mcihangir/camtracker/04_Hardware/PCBs/CamTracker/KiCad_Libs/Components/EMPA/empa_.png

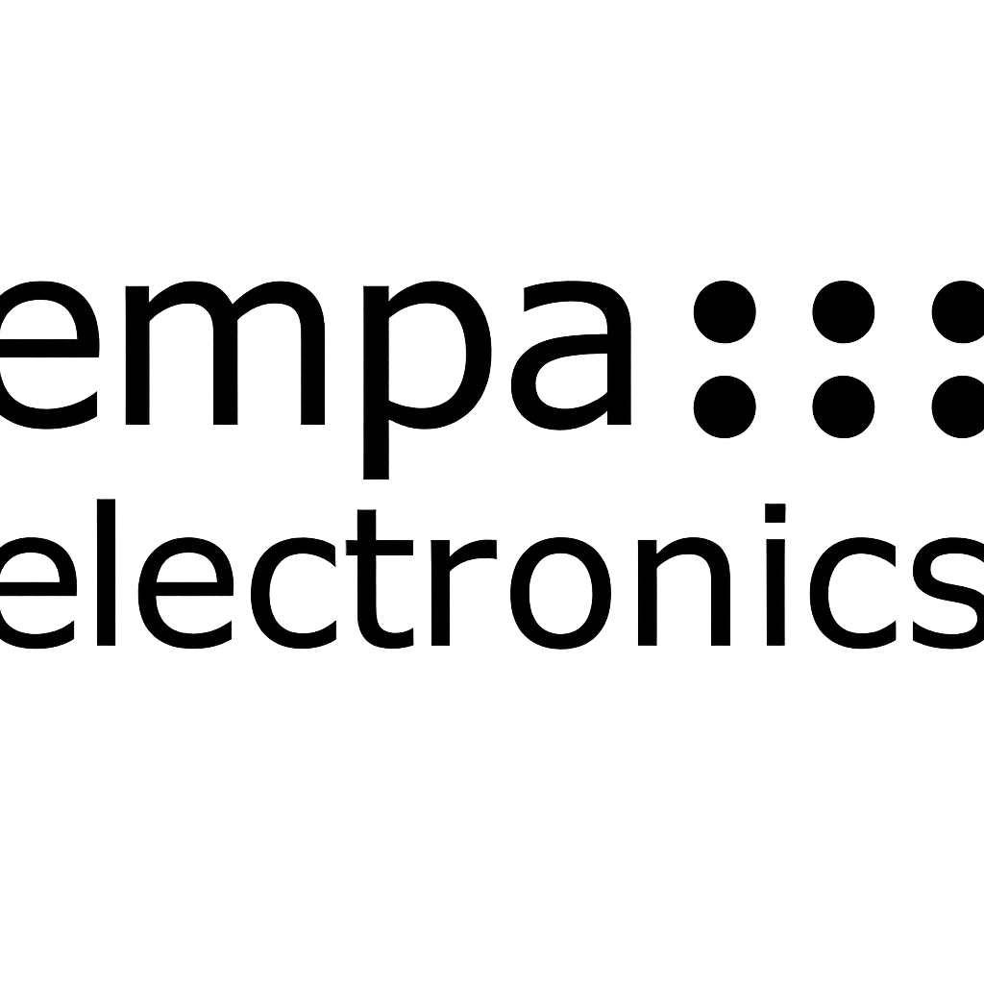
04_Hardware/PCBs/CamTracker/KiCad_Libs/Components/EMPA/empa_.png
