mcihangir/camtracker/04_Hardware/PCBs/CamTracker/KiCad_Libs/Components/C0603C751F5GACTU/3D/C0603C751F5GACTU.stp

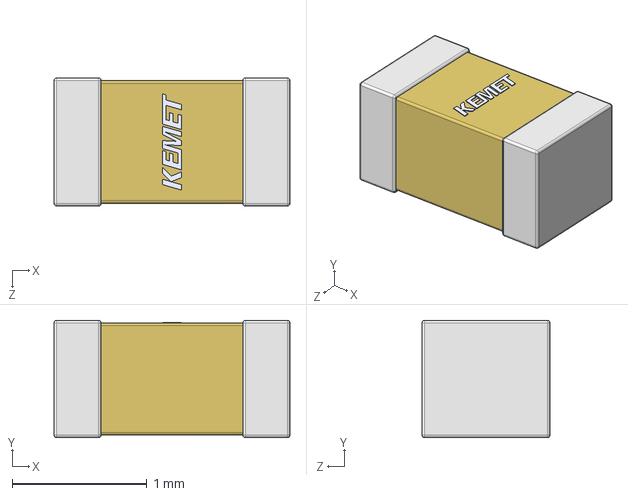
[picture p26: CAD file, 2025-10-18]
04_Hardware/PCBs/CamTracker/KiCad_Libs/Components/C0603C751F5GACTU/3D/C0603C751F5GACTU.stp
1.75 x 0.87 x 0.95 mm
