mcihangir/camtracker/04_Hardware/PCBs/CamTracker/KiCad_Libs/Components/C1608C0G1H102F080AA/3D/C1608C0G1H102F080AA.stp

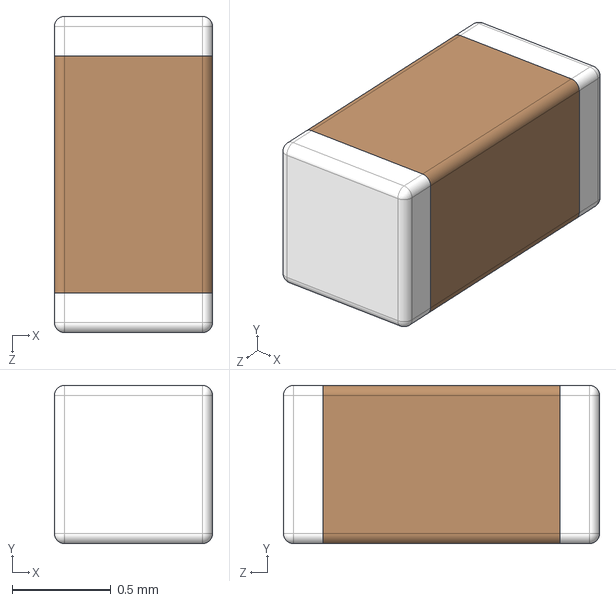
[picture p27: CAD file, 2025-10-18]
04_Hardware/PCBs/CamTracker/KiCad_Libs/Components/C1608C0G1H102F080AA/3D/C1608C0G1H102F080AA.stp
0.8 x 0.8 x 1.60 mm
