mcihangir/camtracker/04_Hardware/PCBs/CamTracker/KiCad_Libs/Components/CRCW08050000Z0EA/3D/CRCW08050000Z0EA.stp

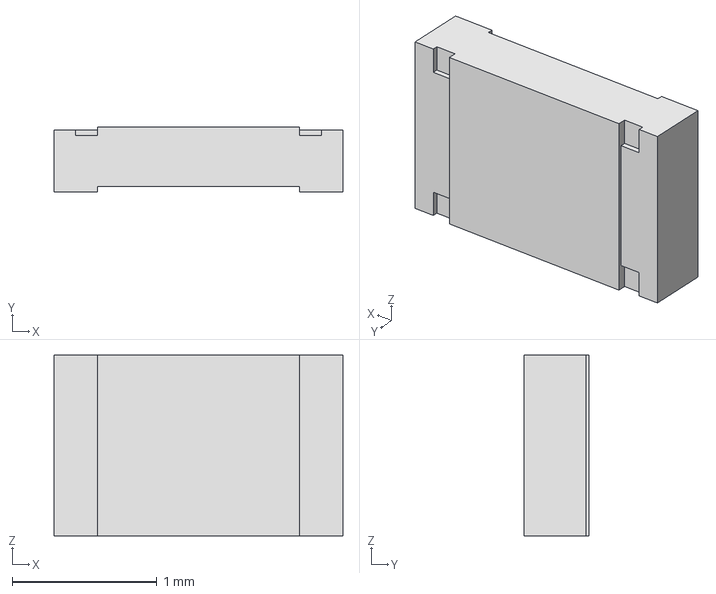
[picture p28: CAD file, 2025-10-18]
04_Hardware/PCBs/CamTracker/KiCad_Libs/Components/CRCW08050000Z0EA/3D/CRCW08050000Z0EA.stp
2.00 x 0.45 x 1.25 mm
