mcihangir/camtracker/04_Hardware/PCBs/CamTracker/KiCad_Libs/Components/CS12ANW03/CS12ANW03/3D/CS12ANW03.stp

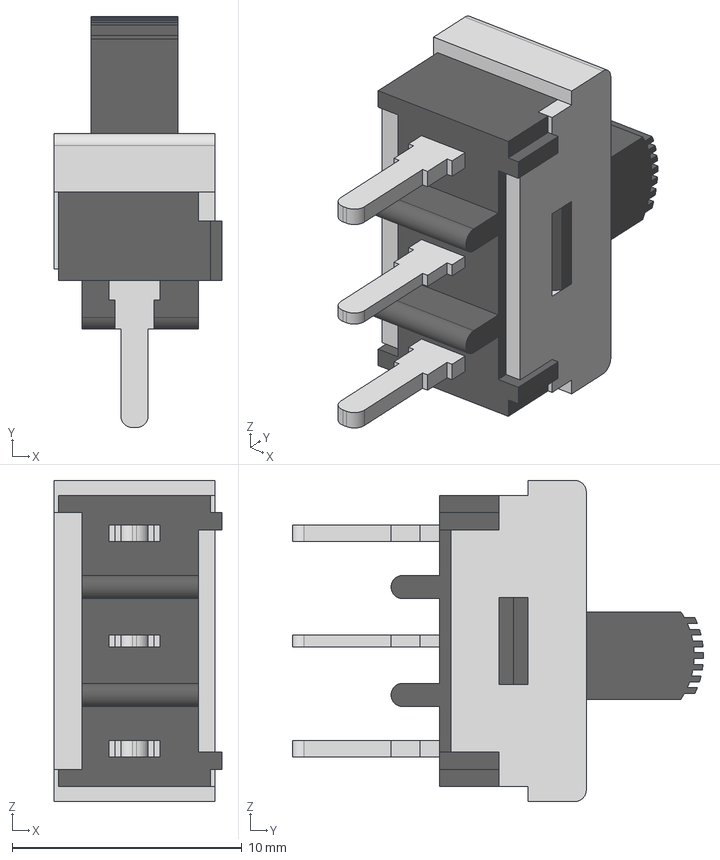
[picture p29: CAD file, 2025-10-18]
04_Hardware/PCBs/CamTracker/KiCad_Libs/Components/CS12ANW03/CS12ANW03/3D/CS12ANW03.stp
7.32 x 17.9 x 14.0 mm
CS12ANW03-body
CS12ANW03-top
CS12ANW03-term
CS12ANW03-slide
