mcihangir/camtracker/04_Hardware/PCBs/CamTracker/KiCad_Libs/Components/ERJ-3GEYJ222V/3D/ERJ-3GEYJ222V.stp

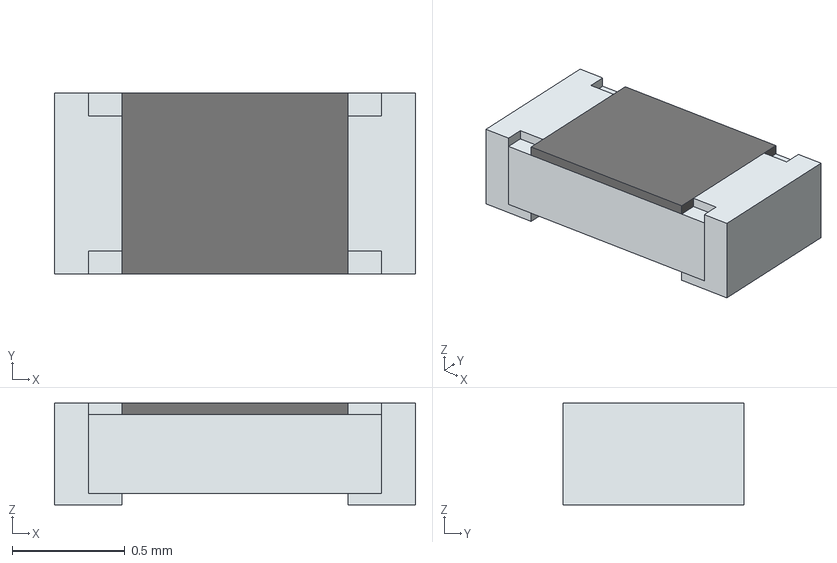
[picture p30: CAD file, 2025-10-18]
04_Hardware/PCBs/CamTracker/KiCad_Libs/Components/ERJ-3GEYJ222V/3D/ERJ-3GEYJ222V.stp
1.60 x 0.8 x 0.45 mm
solidBody
Terminal
solidTop
