mcihangir/camtracker/04_Hardware/PCBs/CamTracker/KiCad_Libs/Components/ESD9B5.0ST5G/ESD9B5.0ST5G.step

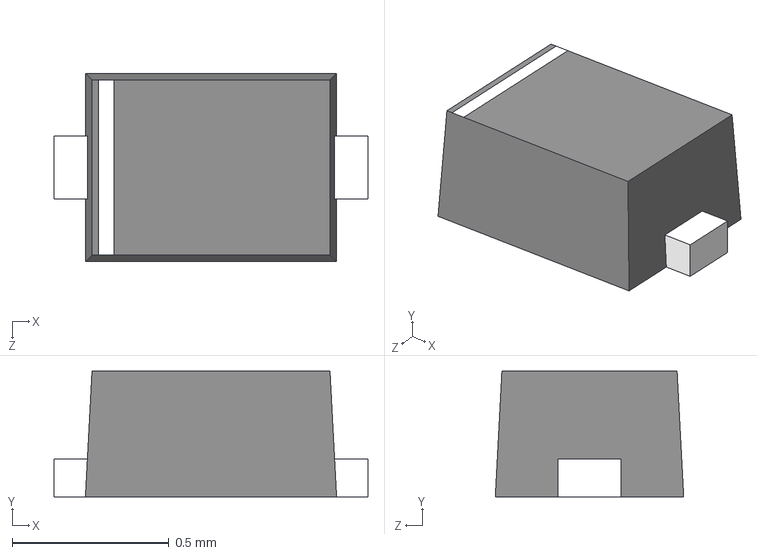
[picture p31: CAD file, 2025-10-18]
04_Hardware/PCBs/CamTracker/KiCad_Libs/Components/ESD9B5.0ST5G/ESD9B5.0ST5G.step
1 x 0.4 x 0.6 mm
