mcihangir/camtracker/04_Hardware/PCBs/CamTracker/KiCad_Libs/Components/FH12-8S-0.5SH_55_/3D/FH12-8S-0.5SH.stp

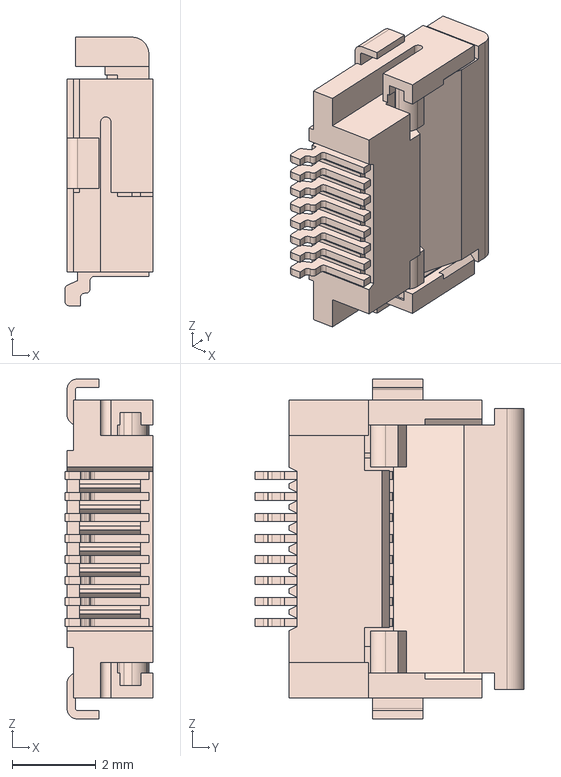
[picture p33: CAD file, 2025-10-18]
04_Hardware/PCBs/CamTracker/KiCad_Libs/Components/FH12-8S-0.5SH_55_/3D/FH12-8S-0.5SH.stp
2.10 x 6.40 x 8.10 mm
