mcihangir/camtracker/04_Hardware/PCBs/CamTracker/KiCad_Libs/Components/FH12S-30S-0.5SH_55_/3D/FH12S-30S-0.5SH_55_.stp

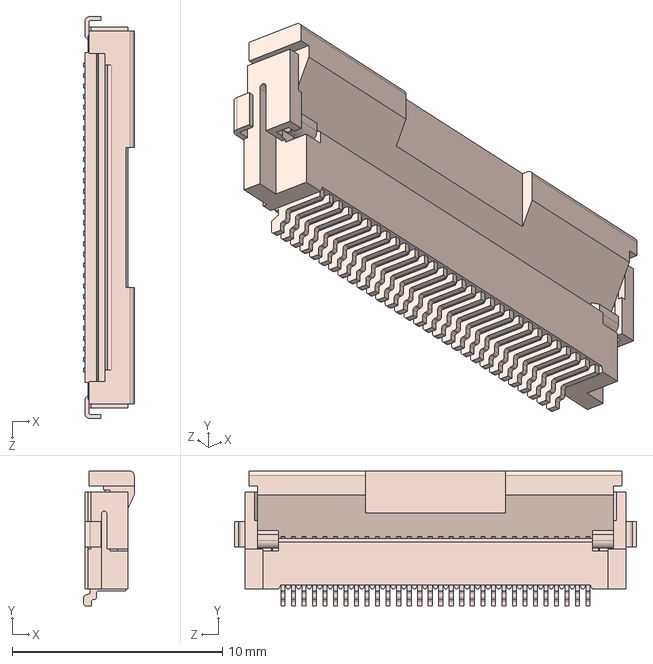
[picture p34: CAD file, 2025-10-18]
04_Hardware/PCBs/CamTracker/KiCad_Libs/Components/FH12S-30S-0.5SH_55_/3D/FH12S-30S-0.5SH_55_.stp
2.40 x 6.40 x 19.1 mm
