mcihangir/camtracker/04_Hardware/PCBs/CamTracker/KiCad_Libs/Components/FH19C-20S-0.5SH_10_/3D/FH19C-20S-0.5SH_10_.stp

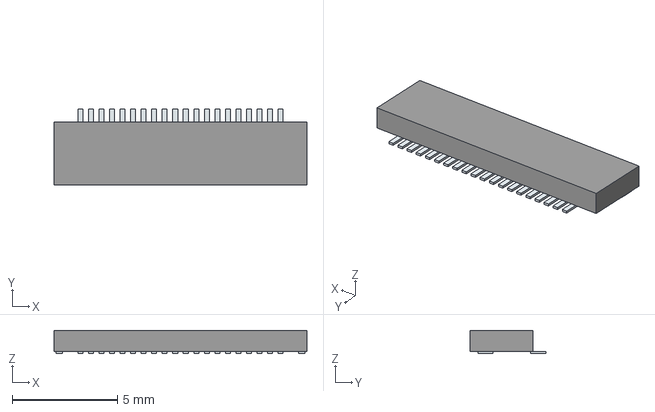
[picture p35: CAD file, 2025-10-18]
04_Hardware/PCBs/CamTracker/KiCad_Libs/Components/FH19C-20S-0.5SH_10_/3D/FH19C-20S-0.5SH_10_.stp
12.0 x 3.62 x 1.10 mm
Pins
