mcihangir/camtracker/04_Hardware/PCBs/CamTracker/KiCad_Libs/Components/FH19SC-30S-0.5SH_09_/3D/FH19C-30S-0.5SH_10_.stp

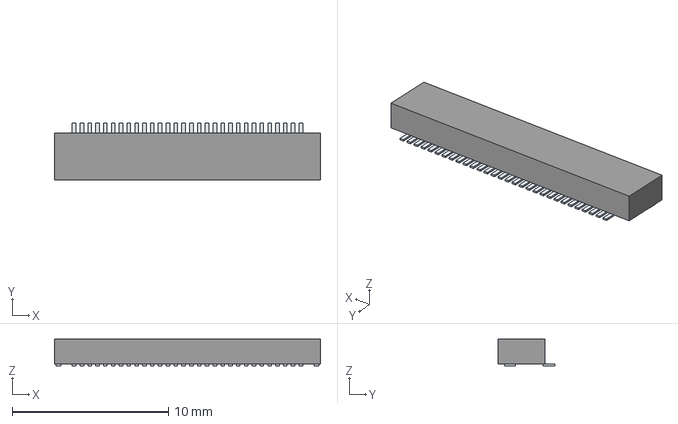
[picture p37: CAD file, 2025-10-18]
04_Hardware/PCBs/CamTracker/KiCad_Libs/Components/FH19SC-30S-0.5SH_09_/3D/FH19C-30S-0.5SH_10_.stp
17.0 x 3.62 x 1.70 mm
Pins
