mcihangir/camtracker/04_Hardware/PCBs/CamTracker/KiCad_Libs/Components/FH35C-27S-0.3SHW_50_/3D/FH35C-27S-0.3SHW-50---3DModel-STEP-1.STEP

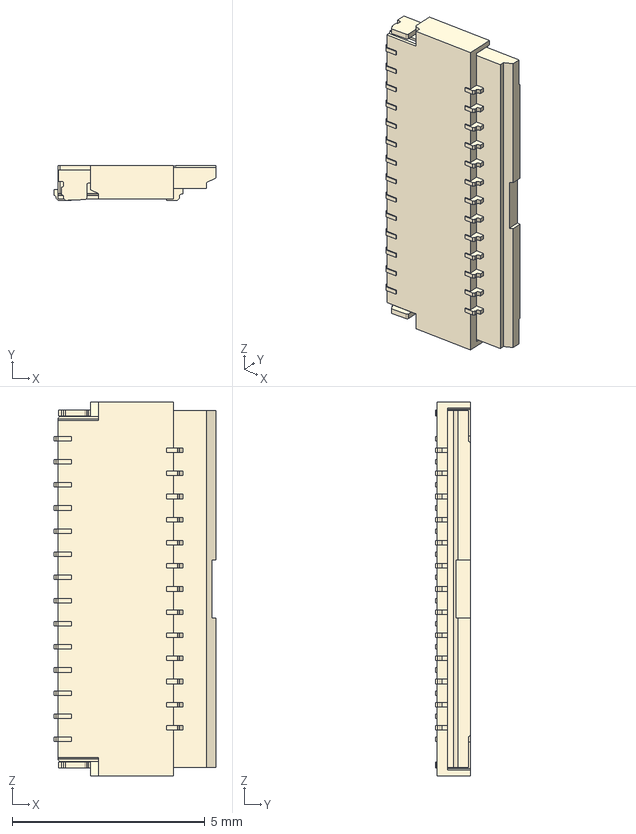
[picture p38: CAD file, 2025-10-18]
04_Hardware/PCBs/CamTracker/KiCad_Libs/Components/FH35C-27S-0.3SHW_50_/3D/FH35C-27S-0.3SHW-50---3DModel-STEP-1.STEP
4.20 x 0.9 x 9.70 mm
