mcihangir/camtracker/04_Hardware/PCBs/CamTracker/KiCad_Libs/Components/GRM1555C1H100JA01D/3D/GRM1555C1H100JA01D.stp

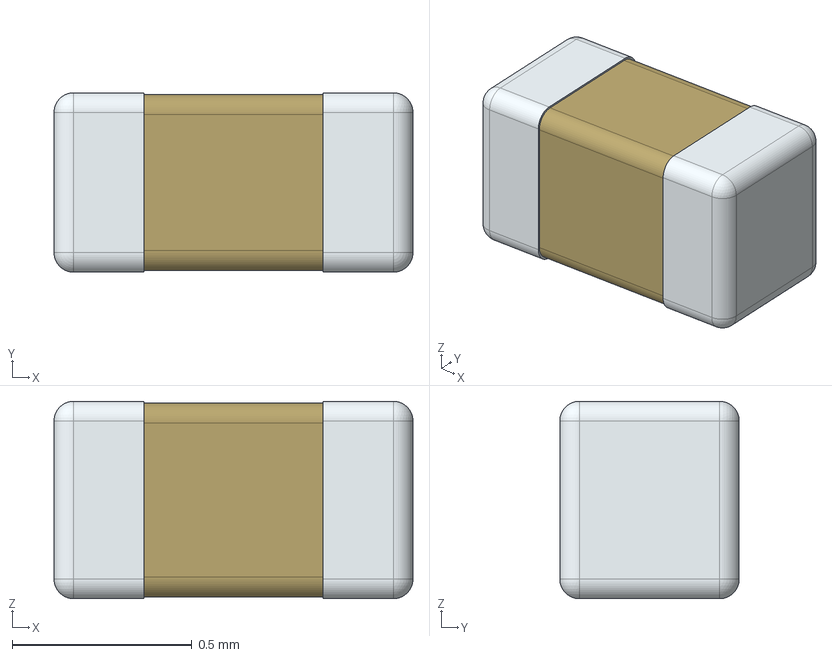
[picture p39: CAD file, 2025-10-18]
04_Hardware/PCBs/CamTracker/KiCad_Libs/Components/GRM1555C1H100JA01D/3D/GRM1555C1H100JA01D.stp
1.00 x 0.5 x 0.55 mm
