mcihangir/camtracker/04_Hardware/PCBs/CamTracker/KiCad_Libs/Components/GRM155R60J475ME47D/3D/GRM155R60J475ME47D.stp

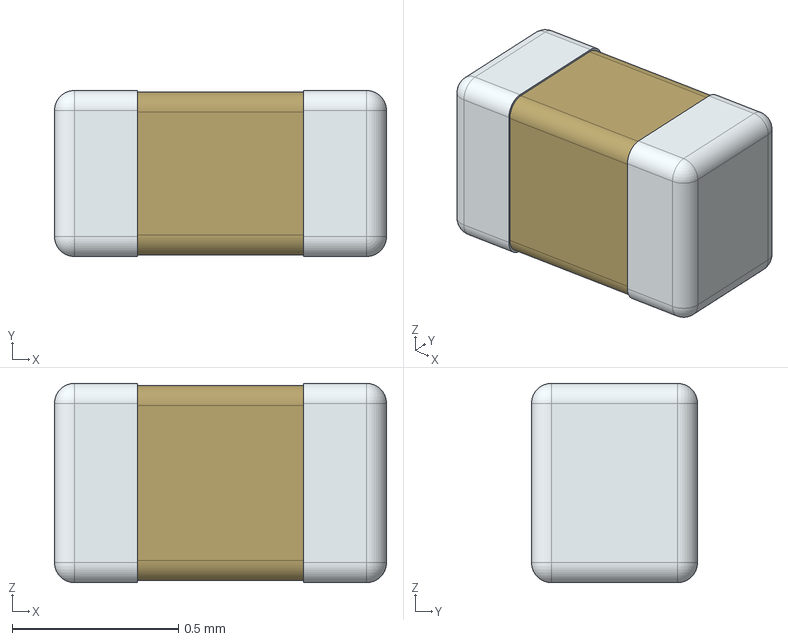
[picture p40: CAD file, 2025-10-18]
04_Hardware/PCBs/CamTracker/KiCad_Libs/Components/GRM155R60J475ME47D/3D/GRM155R60J475ME47D.stp
1.00 x 0.5 x 0.6 mm
