mcihangir/camtracker/04_Hardware/PCBs/CamTracker/KiCad_Libs/Components/GRM155R61H105KE05D/3D/GRM155R61H105KE05D.stp

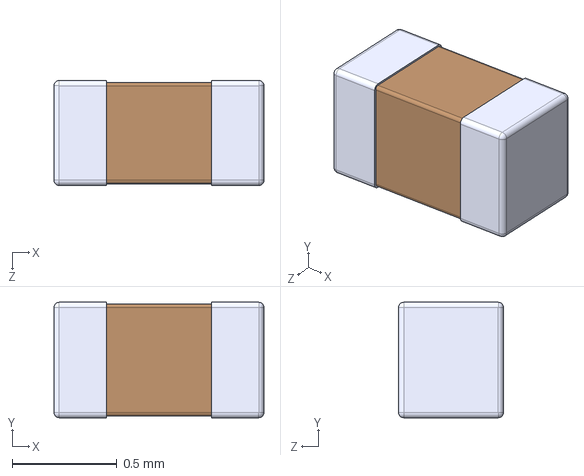
[picture p41: CAD file, 2025-10-18]
04_Hardware/PCBs/CamTracker/KiCad_Libs/Components/GRM155R61H105KE05D/3D/GRM155R61H105KE05D.stp
1.00 x 0.55 x 0.5 mm
