mcihangir/camtracker/04_Hardware/PCBs/CamTracker/KiCad_Libs/Components/GRM21BR61E226ME44L/3D/GRM21BR61E226ME44L.stp

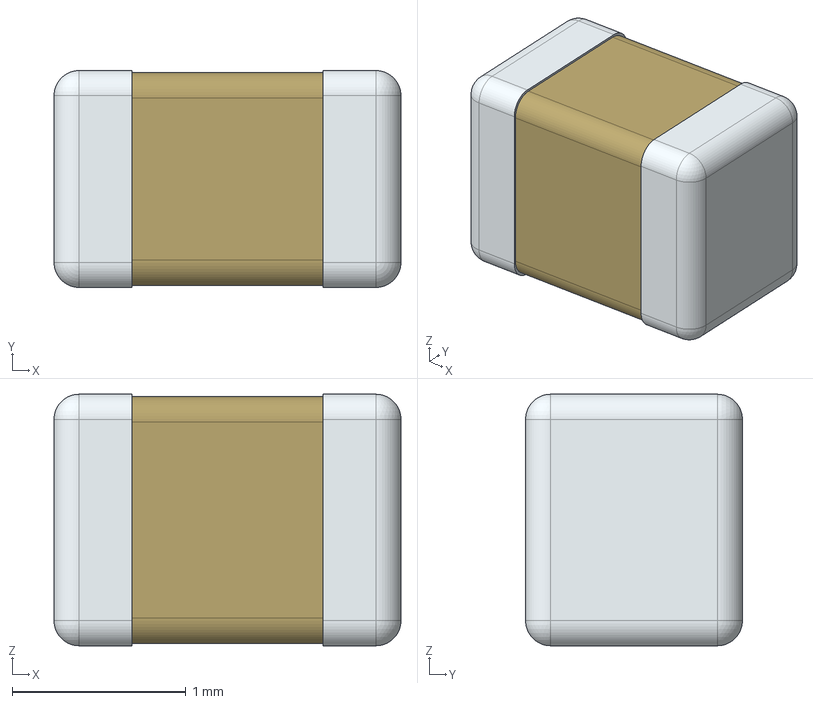
[picture p42: CAD file, 2025-10-18]
04_Hardware/PCBs/CamTracker/KiCad_Libs/Components/GRM21BR61E226ME44L/3D/GRM21BR61E226ME44L.stp
2.00 x 1.25 x 1.45 mm
