mcihangir/camtracker/04_Hardware/PCBs/CamTracker/KiCad_Libs/Components/GRM31CR60J476ME19L/3D/GRM31CR60J476ME19L.stp

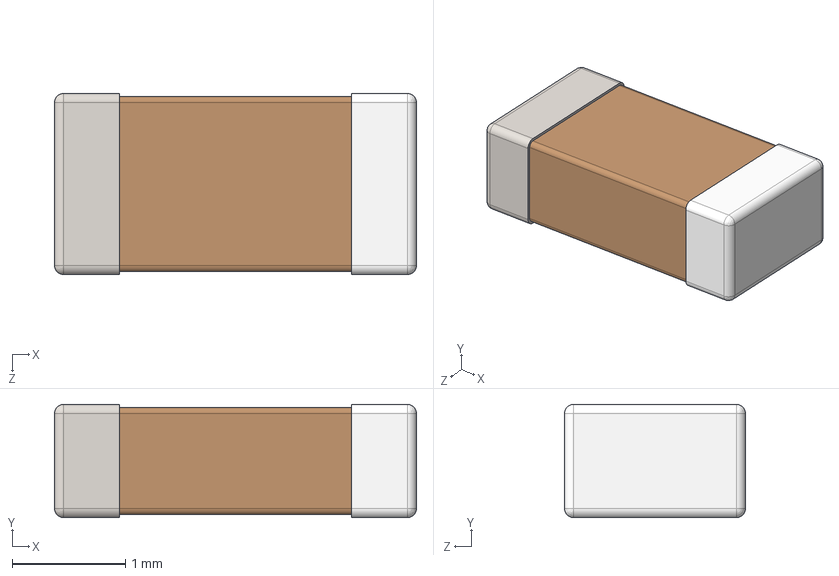
[picture p43: CAD file, 2025-10-18]
04_Hardware/PCBs/CamTracker/KiCad_Libs/Components/GRM31CR60J476ME19L/3D/GRM31CR60J476ME19L.stp
3.20 x 1 x 1.60 mm
GCM31A5C2J820JX01J_3
GCM31A5C2J820JX01J_2
GCM31A5C2J820JX01J
