mcihangir/camtracker/04_Hardware/PCBs/CamTracker/KiCad_Libs/Components/HD-EMB1104-SM-2/HD-EMB1104-SM-2.step

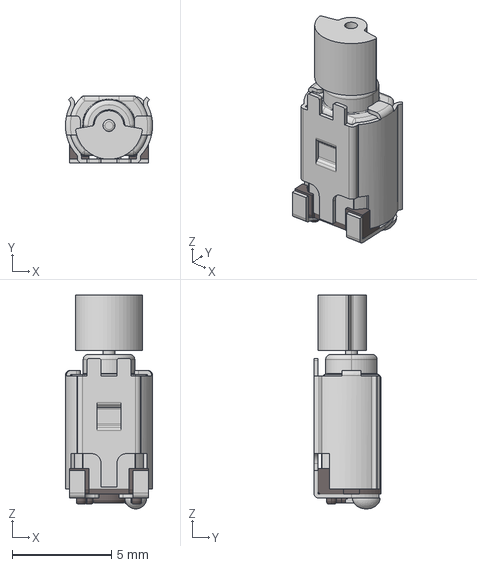
[picture p44: CAD file, 2025-10-18]
04_Hardware/PCBs/CamTracker/KiCad_Libs/Components/HD-EMB1104-SM-2/HD-EMB1104-SM-2.step
4.40 x 3.40 x 10.8 mm
