mcihangir/camtracker/04_Hardware/PCBs/CamTracker/KiCad_Libs/Components/HX JN1.27-2x10 TP H4.9/User Library-KLS1-202C-20-T-B.STEP

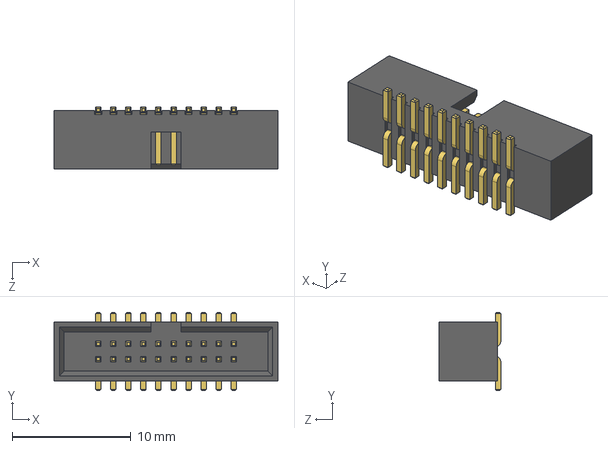
[picture p45: CAD file, 2025-12-15]
04_Hardware/PCBs/CamTracker/KiCad_Libs/Components/HX JN1.27-2x10 TP H4.9/User Library-KLS1-202C-20-T-B.STEP
18.9 x 6.60 x 5.20 mm
