mcihangir/camtracker/04_Hardware/PCBs/CamTracker/KiCad_Libs/Components/L000641/c-l000641-01-1-3d.stp

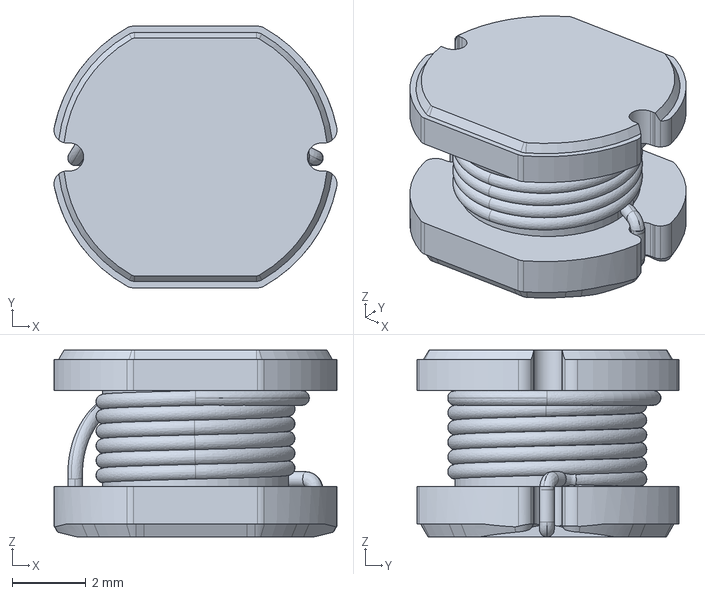
[picture p46: CAD file, 2025-10-18]
04_Hardware/PCBs/CamTracker/KiCad_Libs/Components/L000641/c-l000641-01-1-3d.stp
7.68 x 7.10 x 5.07 mm
