mcihangir/camtracker/04_Hardware/PCBs/CamTracker/KiCad_Libs/Components/LCFE121002A900TG/3D/LCFE121002A900TG.stp

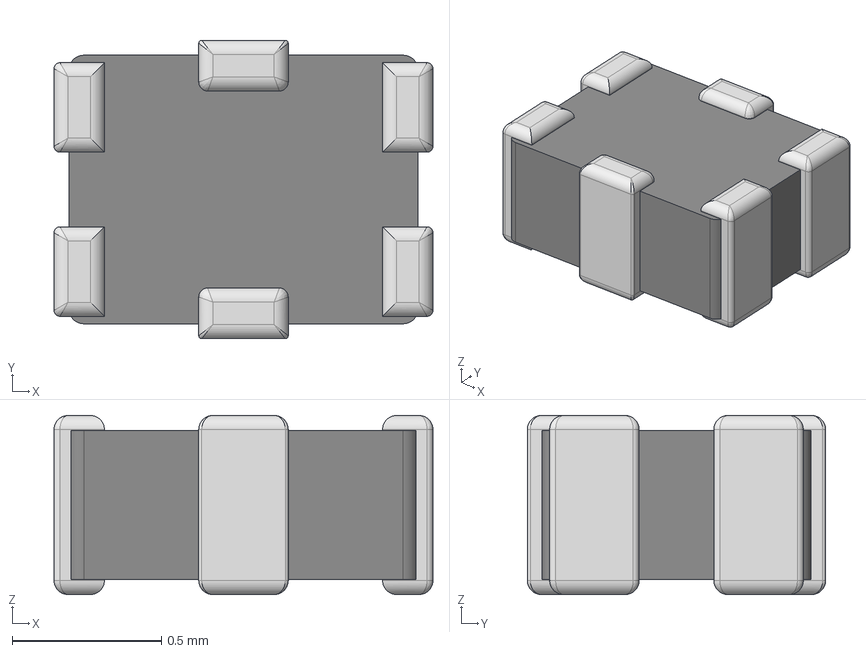
[picture p47: CAD file, 2025-10-18]
04_Hardware/PCBs/CamTracker/KiCad_Libs/Components/LCFE121002A900TG/3D/LCFE121002A900TG.stp
1.27 x 1.00 x 0.6 mm
