mcihangir/camtracker/04_Hardware/PCBs/CamTracker/KiCad_Libs/Components/LIB_22-28-4044/22-28-4044/3D/22-28-4044.stp

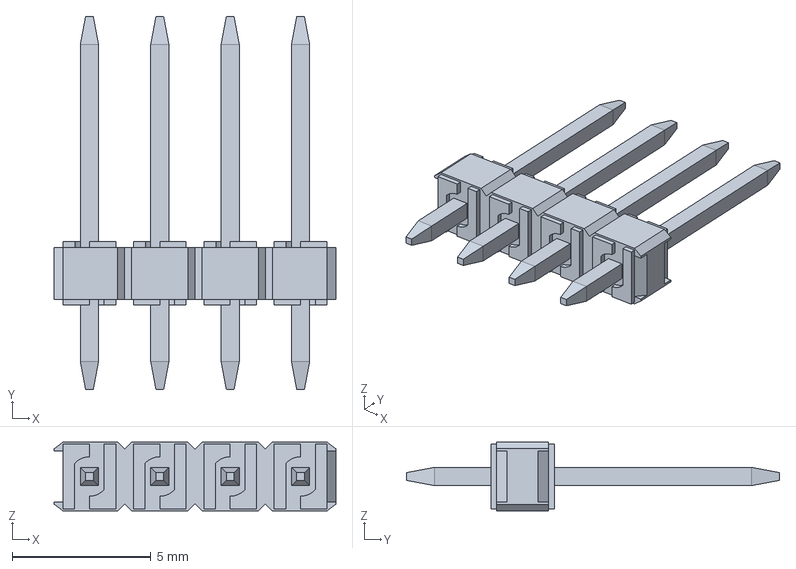
[picture p48: CAD file, 2025-10-18]
04_Hardware/PCBs/CamTracker/KiCad_Libs/Components/LIB_22-28-4044/22-28-4044/3D/22-28-4044.stp
10.2 x 13.5 x 2.49 mm
