mcihangir/camtracker/04_Hardware/PCBs/CamTracker/KiCad_Libs/Components/LIB_25SVPG270M/25SVPG270M/3D/25SVPG270M.stp

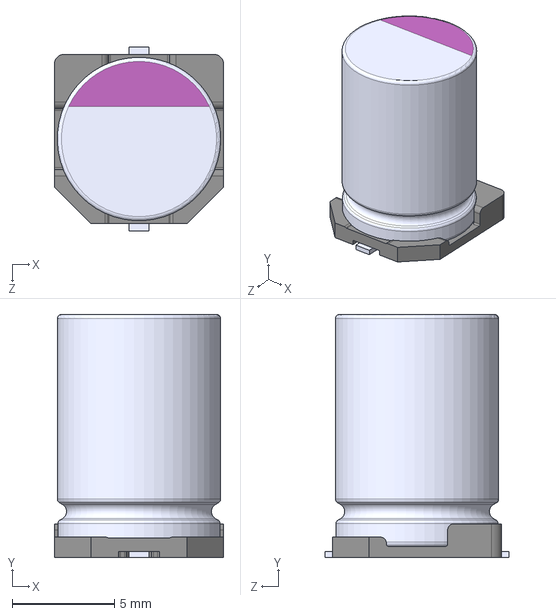
[picture p49: CAD file, 2025-12-18]
04_Hardware/PCBs/CamTracker/KiCad_Libs/Components/LIB_25SVPG270M/25SVPG270M/3D/25SVPG270M.stp
8.30 x 11.9 x 9.00 mm
