mcihangir/camtracker/04_Hardware/PCBs/CamTracker/KiCad_Libs/Components/LIB_2N7002/2N7002/3D/2N7002.stp

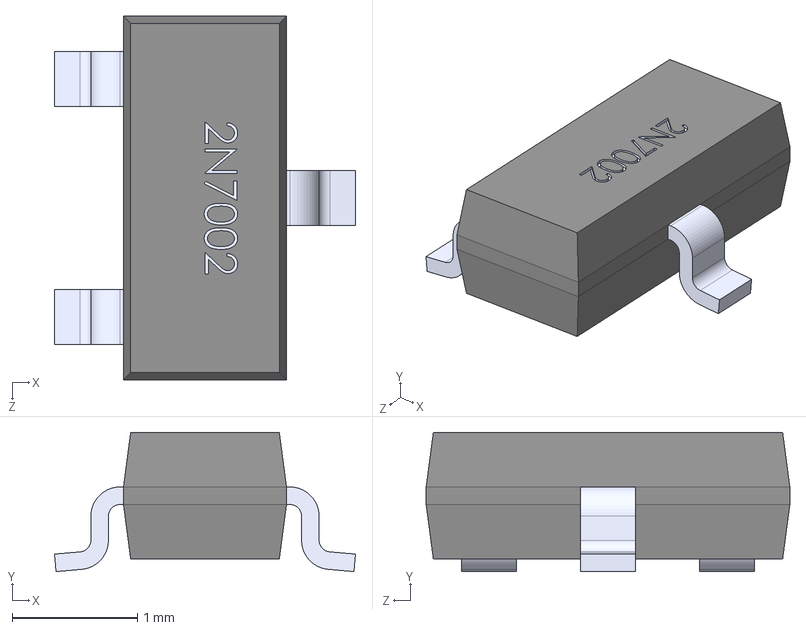
[picture p50: CAD file, 2025-11-17]
04_Hardware/PCBs/CamTracker/KiCad_Libs/Components/LIB_2N7002/2N7002/3D/2N7002.stp
2.40 x 1.11 x 2.90 mm
2N7002_2
2N7002_3
2N7002_4
2N7002
