mcihangir/camtracker/04_Hardware/PCBs/CamTracker/KiCad_Libs/Components/LIB_A765KN227M1CLAE016/A765KN227M1CLAE016/3D/A765KN227M1CLAE016.stp

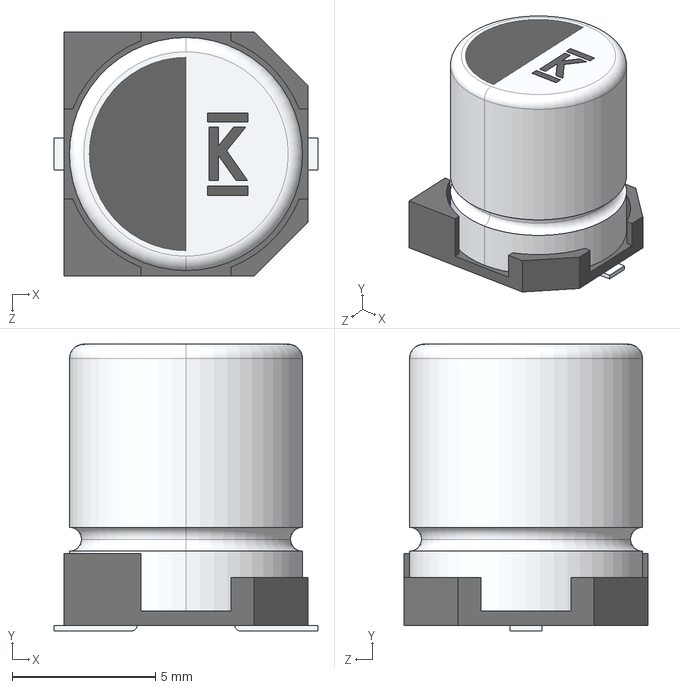
[picture p51: CAD file, 2025-10-29]
04_Hardware/PCBs/CamTracker/KiCad_Libs/Components/LIB_A765KN227M1CLAE016/A765KN227M1CLAE016/3D/A765KN227M1CLAE016.stp
9.20 x 10.0 x 8.50 mm
