mcihangir/camtracker/04_Hardware/PCBs/CamTracker/KiCad_Libs/Components/LIB_ABM8-272-T3/ABM8-272-T3/3D/ABM8-272-T3.stp

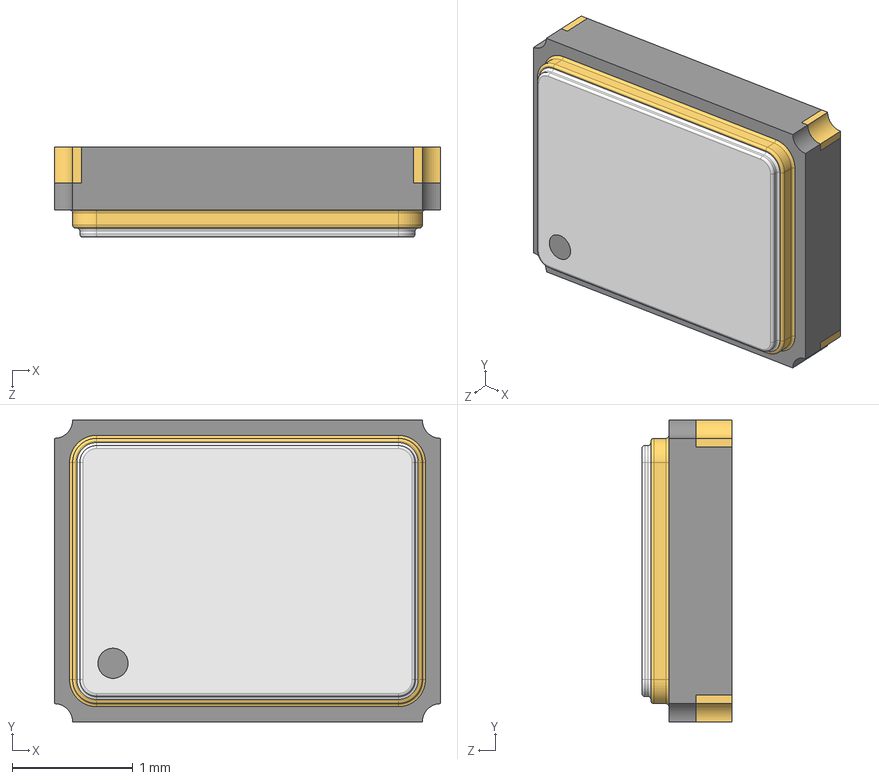
[picture p52: CAD file, 2025-10-18]
04_Hardware/PCBs/CamTracker/KiCad_Libs/Components/LIB_ABM8-272-T3/ABM8-272-T3/3D/ABM8-272-T3.stp
3.20 x 2.50 x 0.75 mm
