mcihangir/camtracker/04_Hardware/PCBs/CamTracker/KiCad_Libs/Components/LIB_AP7179DSKZ20-13/AP7179DSKZ20-13/3D/AP7179DSKZ20-13.stp

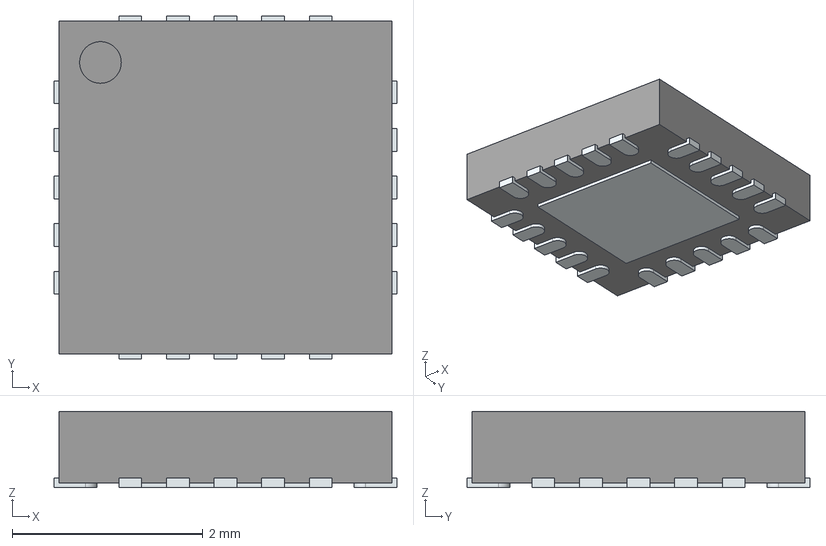
[picture p53: CAD file, 2025-10-18]
04_Hardware/PCBs/CamTracker/KiCad_Libs/Components/LIB_AP7179DSKZ20-13/AP7179DSKZ20-13/3D/AP7179DSKZ20-13.stp
3.60 x 3.60 x 0.8 mm
ThermalPin
PinsArrayLR
PinsArrayTB
