mcihangir/camtracker/04_Hardware/PCBs/CamTracker/KiCad_Libs/Components/LIB_AP7361E-33FGE-7/AP7361E-33FGE-7/3D/AP7361E-33FGE-7.stp

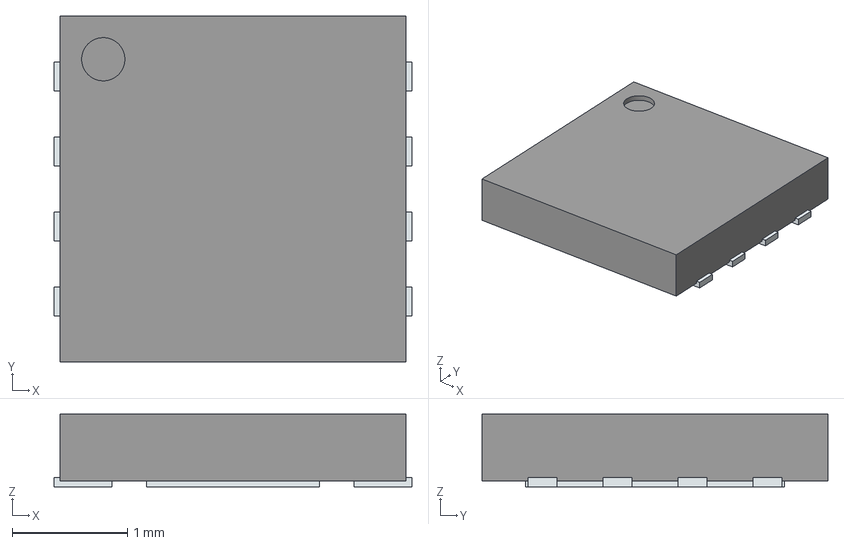
[picture p54: CAD file, 2025-10-29]
04_Hardware/PCBs/CamTracker/KiCad_Libs/Components/LIB_AP7361E-33FGE-7/AP7361E-33FGE-7/3D/AP7361E-33FGE-7.stp
3.10 x 3.00 x 0.63 mm
ThermalPin
PinsArrayLR
