mcihangir/camtracker/04_Hardware/PCBs/CamTracker/KiCad_Libs/Components/LIB_AP7362-33SP-13/AP7362-33SP-13/3D/AP7362-33SP-13.stp

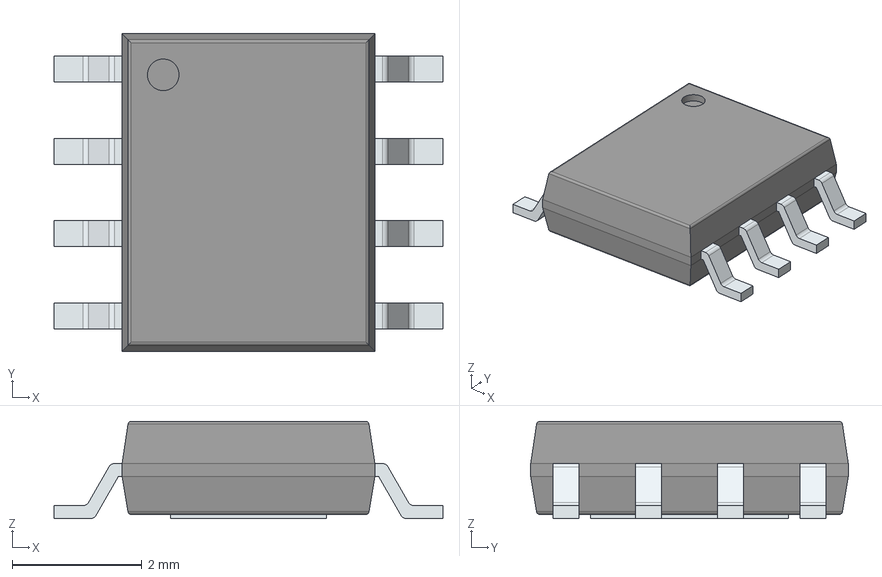
[picture p55: CAD file, 2025-10-29]
04_Hardware/PCBs/CamTracker/KiCad_Libs/Components/LIB_AP7362-33SP-13/AP7362-33SP-13/3D/AP7362-33SP-13.stp
6.00 x 4.90 x 1.50 mm
PinsArrayLR
ThermalPad
