mcihangir/camtracker/04_Hardware/PCBs/CamTracker/KiCad_Libs/Components/LIB_CGA6P1X7S1A476M250AC/CGA6P1X7S1A476M250AC/3D/CGA6P1X7S1A476M250AC.stp

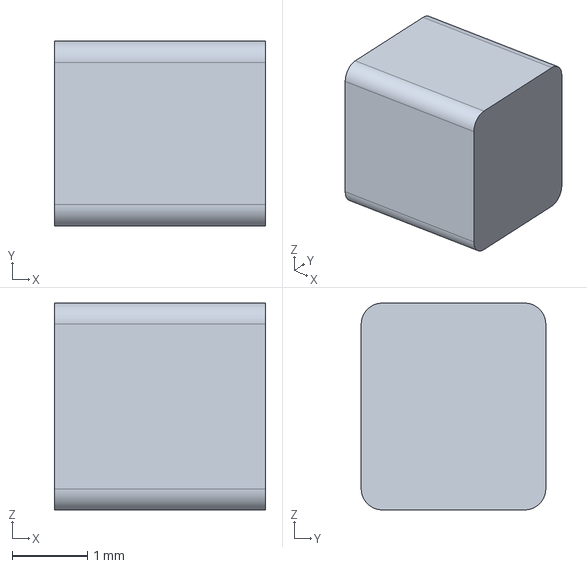
[picture p56: CAD file, 2025-10-18]
04_Hardware/PCBs/CamTracker/KiCad_Libs/Components/LIB_CGA6P1X7S1A476M250AC/CGA6P1X7S1A476M250AC/3D/CGA6P1X7S1A476M250AC.stp
2.80 x 2.45 x 2.74 mm
