mcihangir/camtracker/04_Hardware/PCBs/CamTracker/KiCad_Libs/Components/LIB_CL31B106KBK6PJE/CL31B106KBK6PJE/3D/CL31B106KBK6PJE.stp

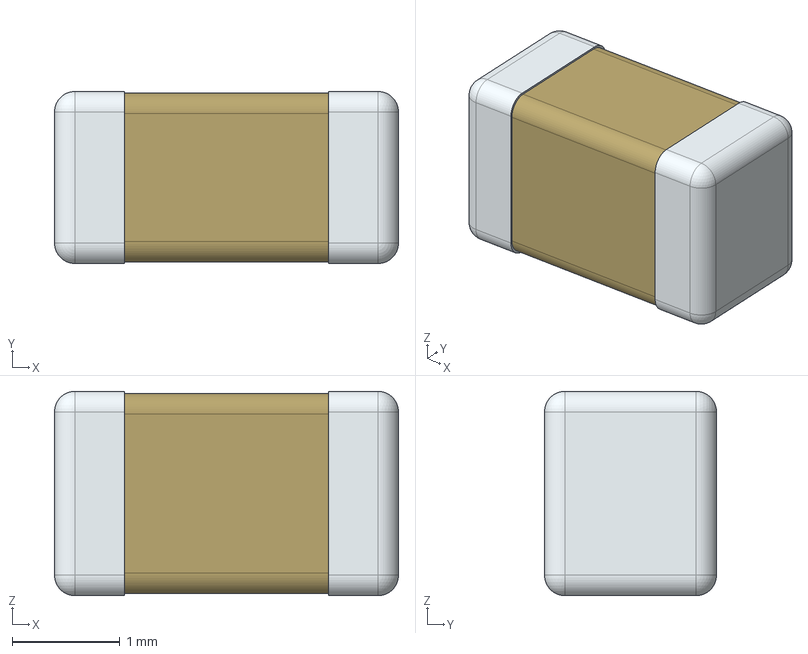
[picture p57: CAD file, 2025-10-18]
04_Hardware/PCBs/CamTracker/KiCad_Libs/Components/LIB_CL31B106KBK6PJE/CL31B106KBK6PJE/3D/CL31B106KBK6PJE.stp
3.20 x 1.60 x 1.90 mm
