mcihangir/camtracker/04_Hardware/PCBs/CamTracker/KiCad_Libs/Components/LIB_CMM-3729AT-42316-TR/CMM-3729AT-42316-TR/3D/CMM-3729AT-42316-TR.stp

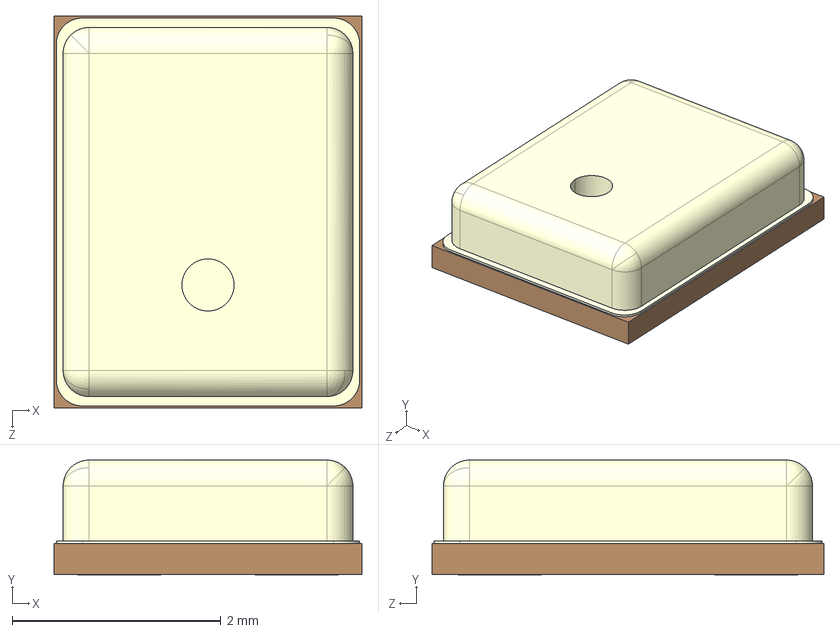
[picture p58: CAD file, 2025-10-18]
04_Hardware/PCBs/CamTracker/KiCad_Libs/Components/LIB_CMM-3729AT-42316-TR/CMM-3729AT-42316-TR/3D/CMM-3729AT-42316-TR.stp
2.95 x 1.10 x 3.76 mm
