mcihangir/camtracker/04_Hardware/PCBs/CamTracker/KiCad_Libs/Components/LIB_EEH-ZU1V471UP/EEH-ZU1V471UP/3D/EEH-ZU1V471UP.stp

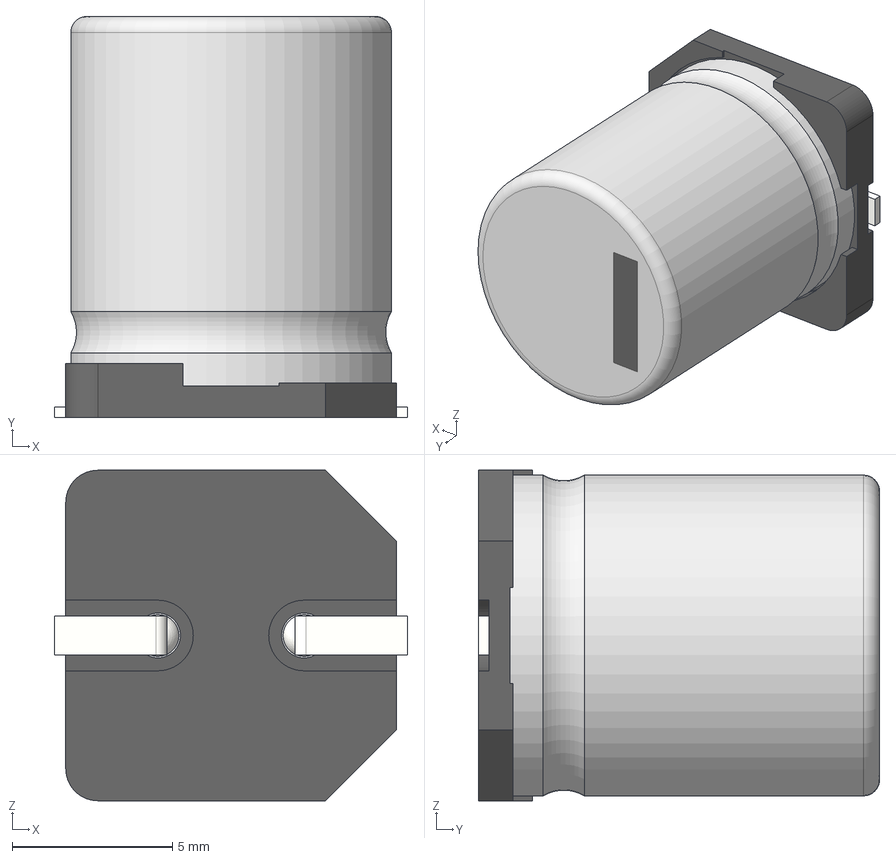
[picture p59: CAD file, 2025-12-15]
04_Hardware/PCBs/CamTracker/KiCad_Libs/Components/LIB_EEH-ZU1V471UP/EEH-ZU1V471UP/3D/EEH-ZU1V471UP.stp
11.0 x 12.5 x 10.3 mm
標準品ケースΦ10x11.52L SIDE CODE G12
標準品座版Φ10 SIZE CODE G12
標準品リード線Φ10 SIZE CODE G1 2 x 2
