mcihangir/camtracker/04_Hardware/PCBs/CamTracker/KiCad_Libs/Components/LIB_ETQ-P4M6R8KVC/ETQ-P4M6R8KVC/3D/ETQ-P4M6R8KVC.stp

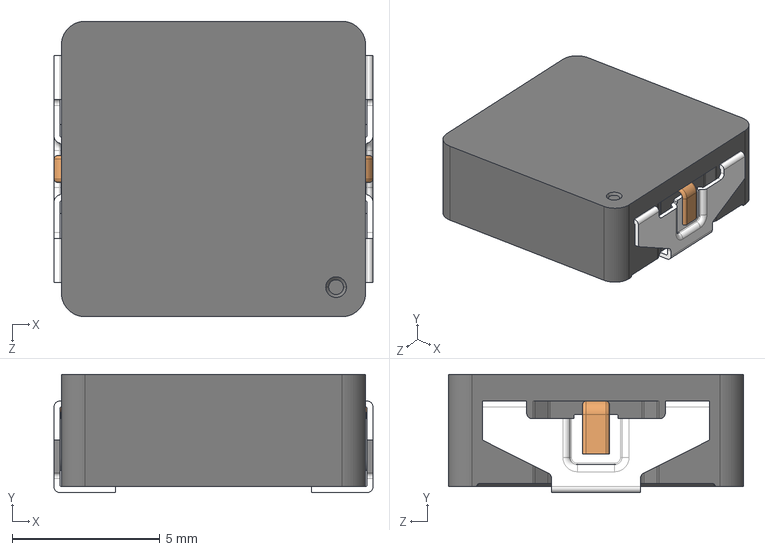
[picture p60: CAD file, 2025-10-18]
04_Hardware/PCBs/CamTracker/KiCad_Libs/Components/LIB_ETQ-P4M6R8KVC/ETQ-P4M6R8KVC/3D/ETQ-P4M6R8KVC.stp
10.8 x 4.00 x 10.0 mm
