mcihangir/camtracker/04_Hardware/PCBs/CamTracker/KiCad_Libs/Components/LIB_ETQ-P4M6R8KVK/ETQ-P4M6R8KVK/3D/ETQ-P4M6R8KVK.stp

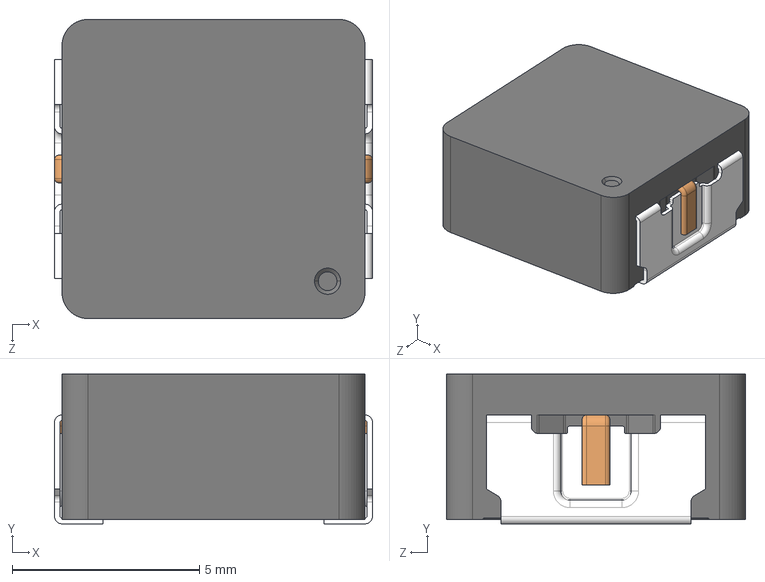
[picture p61: CAD file, 2025-10-18]
04_Hardware/PCBs/CamTracker/KiCad_Libs/Components/LIB_ETQ-P4M6R8KVK/ETQ-P4M6R8KVK/3D/ETQ-P4M6R8KVK.stp
8.50 x 4.00 x 8.00 mm
