mcihangir/camtracker/04_Hardware/PCBs/CamTracker/KiCad_Libs/Components/LIB_LSEUC3225HKT1R0M/LSEUC3225HKT1R0M/3D/LSEUC3225HKT1R0M.stp

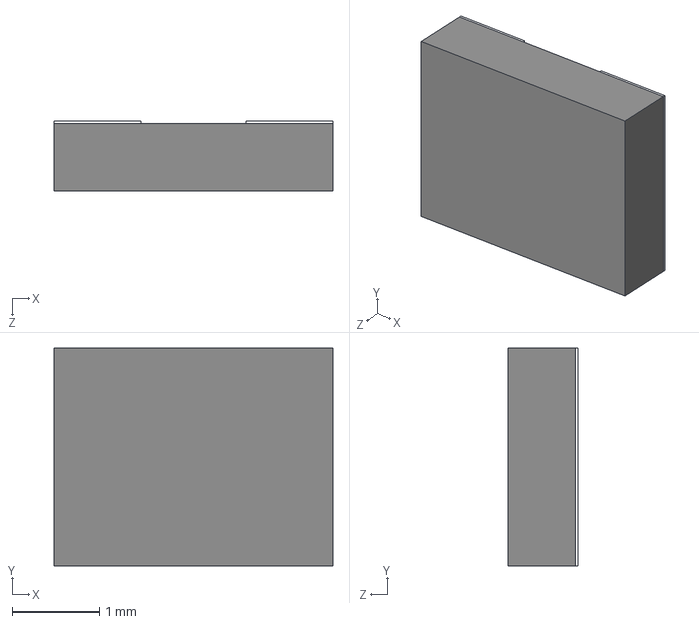
[picture p62: CAD file, 2025-10-29]
04_Hardware/PCBs/CamTracker/KiCad_Libs/Components/LIB_LSEUC3225HKT1R0M/LSEUC3225HKT1R0M/3D/LSEUC3225HKT1R0M.stp
3.20 x 2.50 x 0.8 mm
