mcihangir/camtracker/04_Hardware/PCBs/CamTracker/KiCad_Libs/Components/LIB_MEM2061-01-188-00-A/MEM2061-01-188-00-A/3D/MEM2061-01-188-00-A.stp

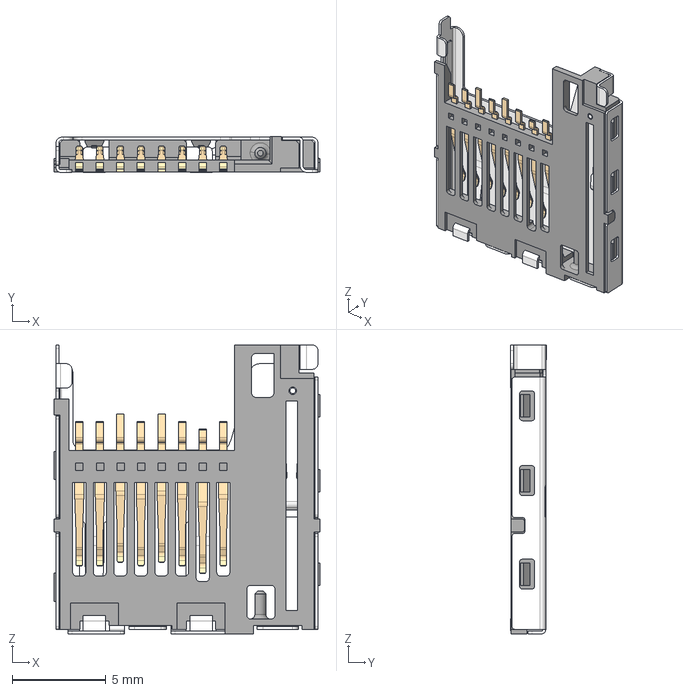
[picture p63: CAD file, 2025-10-18]
04_Hardware/PCBs/CamTracker/KiCad_Libs/Components/LIB_MEM2061-01-188-00-A/MEM2061-01-188-00-A/3D/MEM2061-01-188-00-A.stp
14.2 x 1.95 x 15.5 mm
MEM2061-01-188-00-A_PART2
MEM2061-01-188-00-A_PART1
