mcihangir/camtracker/04_Hardware/PCBs/CamTracker/KiCad_Libs/Components/LIB_PI3USB4000DZUAEX/PI3USB4000DZUAEX/3D/PI3USB4000DZUAEX.stp

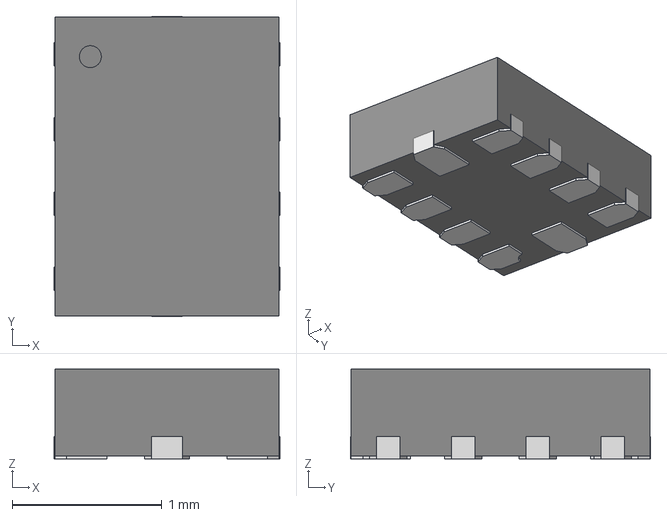
[picture p64: CAD file, 2025-10-18]
04_Hardware/PCBs/CamTracker/KiCad_Libs/Components/LIB_PI3USB4000DZUAEX/PI3USB4000DZUAEX/3D/PI3USB4000DZUAEX.stp
1.51 x 2.00 x 0.6 mm
