mcihangir/camtracker/04_Hardware/PCBs/CamTracker/KiCad_Libs/Components/LIB_PN7160B1HN_C100E/PN7160B1HN_C100E/3D/PN7160B1HN_C100E.stp

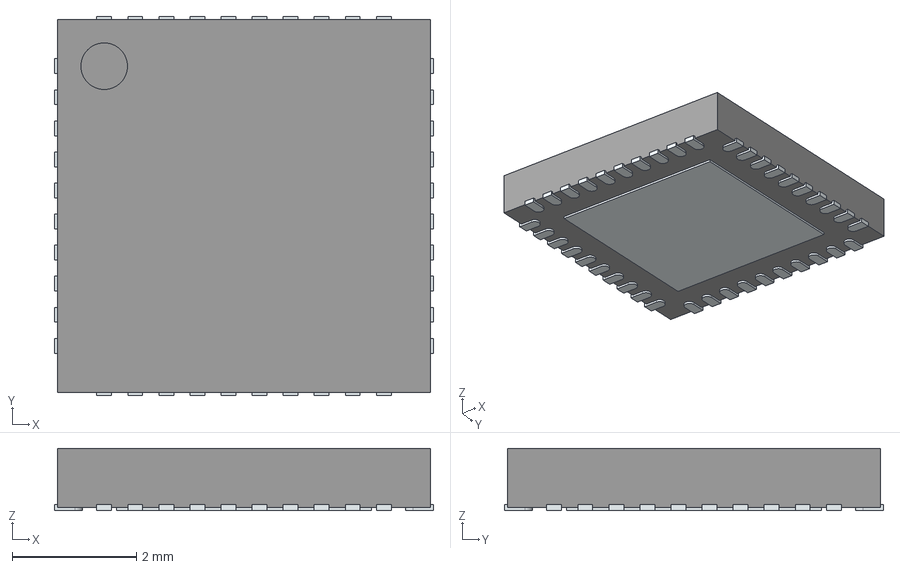
[picture p65: CAD file, 2025-10-18]
04_Hardware/PCBs/CamTracker/KiCad_Libs/Components/LIB_PN7160B1HN_C100E/PN7160B1HN_C100E/3D/PN7160B1HN_C100E.stp
6.10 x 6.10 x 1.00 mm
ThermalPin
PinsArrayLR
PinsArrayTB
