mcihangir/camtracker/04_Hardware/PCBs/CamTracker/KiCad_Libs/Components/LIB_PZT3904T1G/PZT3904T1G/3D/PZT3904T1G.stp

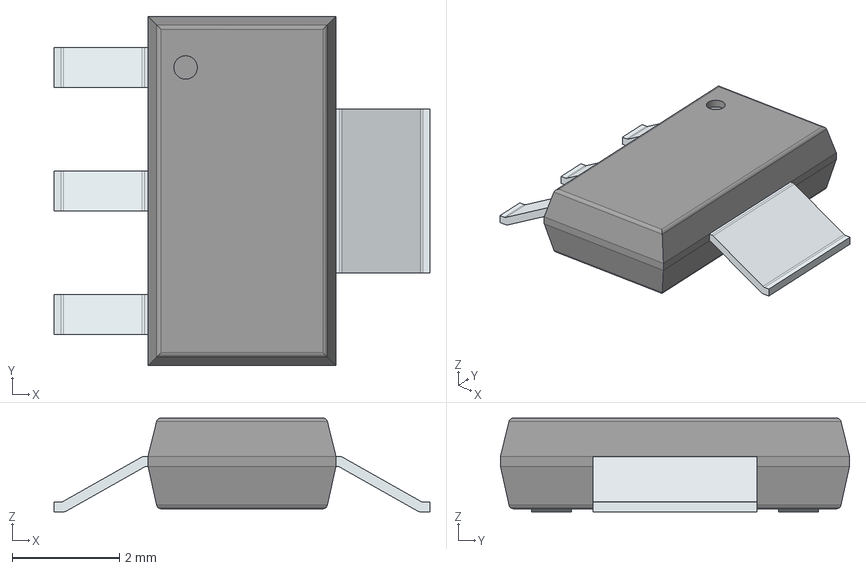
[picture p66: CAD file, 2025-10-18]
04_Hardware/PCBs/CamTracker/KiCad_Libs/Components/LIB_PZT3904T1G/PZT3904T1G/3D/PZT3904T1G.stp
7.00 x 6.50 x 1.75 mm
PinsArrayL
FilletPinR
