mcihangir/camtracker/04_Hardware/PCBs/CamTracker/KiCad_Libs/Components/LIB_RQ7E100ATTCR/RQ7E100ATTCR/3D/RQ7E100ATTCR.stp

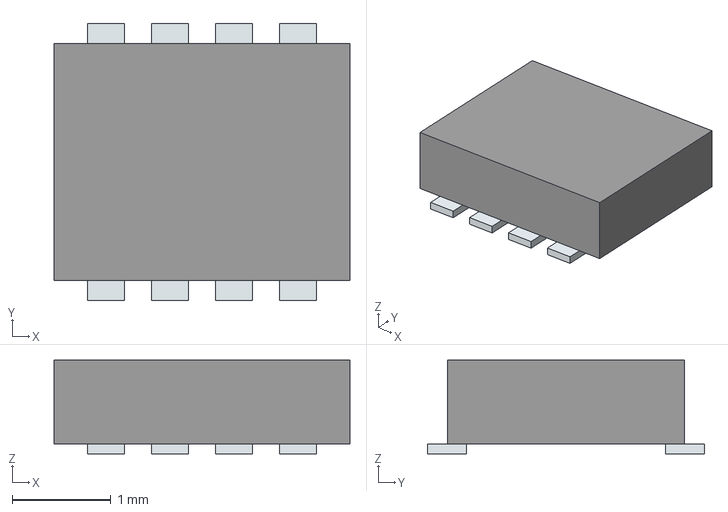
[picture p67: CAD file, 2025-11-16]
04_Hardware/PCBs/CamTracker/KiCad_Libs/Components/LIB_RQ7E100ATTCR/RQ7E100ATTCR/3D/RQ7E100ATTCR.stp
3.00 x 2.81 x 0.95 mm
Pins
