mcihangir/camtracker/04_Hardware/PCBs/CamTracker/KiCad_Libs/Components/LIB_SC0914_7_/SC0914_7_/3D/SC0914_7_.stp

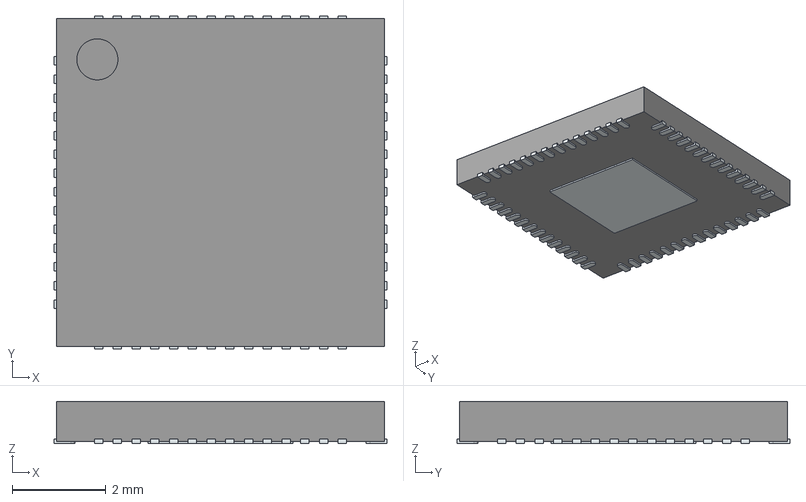
[picture p68: CAD file, 2025-10-18]
04_Hardware/PCBs/CamTracker/KiCad_Libs/Components/LIB_SC0914_7_/SC0914_7_/3D/SC0914_7_.stp
7.10 x 7.10 x 0.9 mm
ThermalPin
PinsArrayLR
PinsArrayTB
