mcihangir/camtracker/04_Hardware/PCBs/CamTracker/KiCad_Libs/Components/LIB_SHF-108-01-L-D-SM/SHF-108-01-L-D-SM/3D/SHF-108-01-L-D-SM-TR.stp

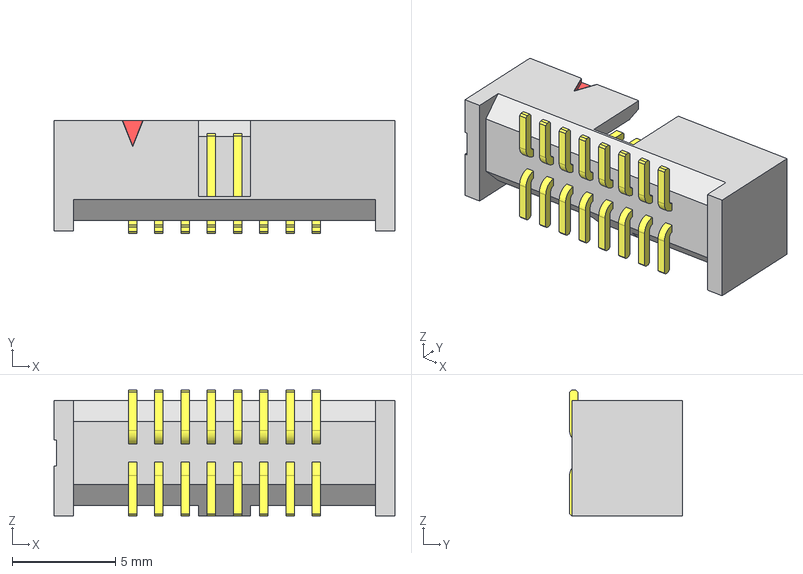
[picture p69: CAD file, 2025-11-14]
04_Hardware/PCBs/CamTracker/KiCad_Libs/Components/LIB_SHF-108-01-L-D-SM/SHF-108-01-L-D-SM/3D/SHF-108-01-L-D-SM-TR.stp
16.5 x 5.46 x 6.10 mm
SHF-108-01-D_header
SHF-First_Position_Indicator
T-1S71-02-08-D-SM
