mcihangir/camtracker/04_Hardware/PCBs/CamTracker/KiCad_Libs/Components/LIB_SMBJ20A/SMBJ20A/3D/SMBJ20A.stp

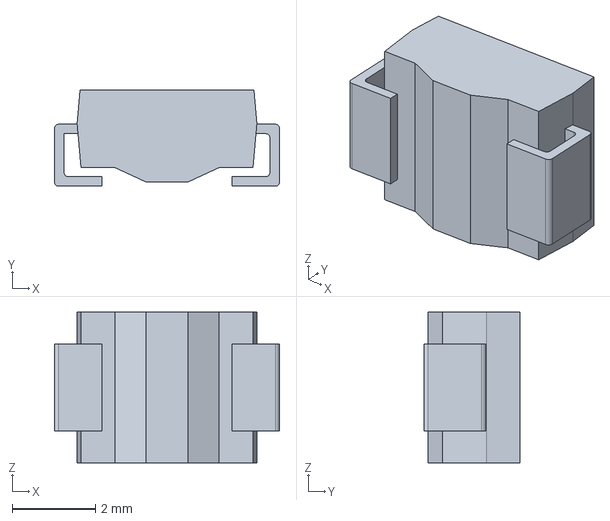
[picture p70: CAD file, 2025-10-18]
04_Hardware/PCBs/CamTracker/KiCad_Libs/Components/LIB_SMBJ20A/SMBJ20A/3D/SMBJ20A.stp
5.40 x 2.31 x 3.62 mm
