mcihangir/camtracker/04_Hardware/PCBs/CamTracker/KiCad_Libs/Components/LIB_USB3076-30-A/USB3076-30-A/3D/USB3076-30-A.stp

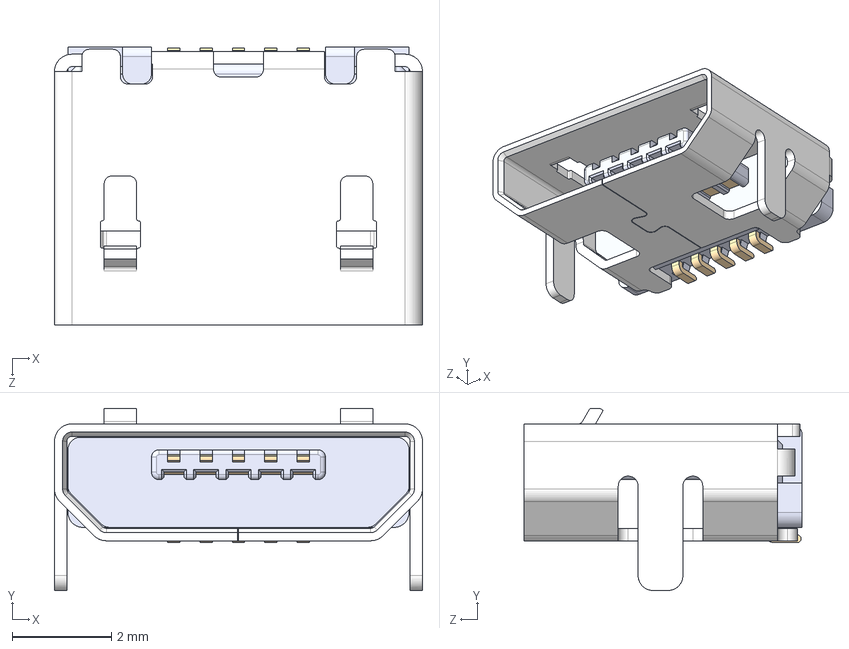
[picture p71: CAD file, 2025-10-18]
04_Hardware/PCBs/CamTracker/KiCad_Libs/Components/LIB_USB3076-30-A/USB3076-30-A/3D/USB3076-30-A.stp
7.40 x 3.66 x 5.60 mm
USB3076-30-A_PART2
USB3076-30-A_PART1
