mcihangir/camtracker/04_Hardware/PCBs/CamTracker/KiCad_Libs/Components/LIB_W25Q128JVSIM/W25Q128JVSIM/3D/W25Q128JVSIM.stp

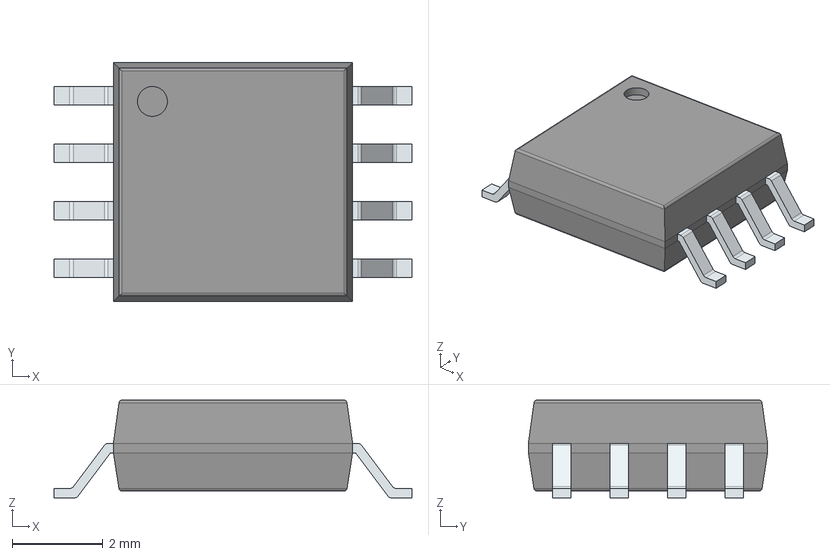
[picture p72: CAD file, 2025-10-18]
04_Hardware/PCBs/CamTracker/KiCad_Libs/Components/LIB_W25Q128JVSIM/W25Q128JVSIM/3D/W25Q128JVSIM.stp
7.90 x 5.28 x 2.16 mm
PinsArrayLR
