mcihangir/camtracker/04_Hardware/PCBs/CamTracker/KiCad_Libs/Components/LIS2DH12TR/LIS2DH12TR.stp

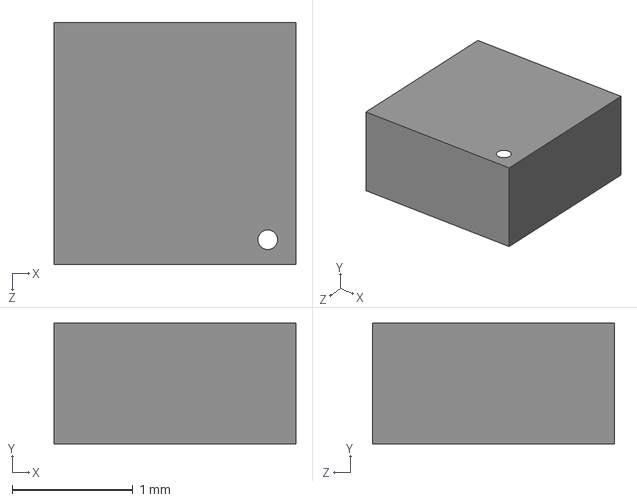
[picture p73: CAD file, 2025-10-18]
04_Hardware/PCBs/CamTracker/KiCad_Libs/Components/LIS2DH12TR/LIS2DH12TR.stp
2.00 x 1.00 x 2.00 mm
