mcihangir/camtracker/04_Hardware/PCBs/CamTracker/KiCad_Libs/Components/LMK107BJ475KA-T/3D/LMK107BJ475KA-T.stp

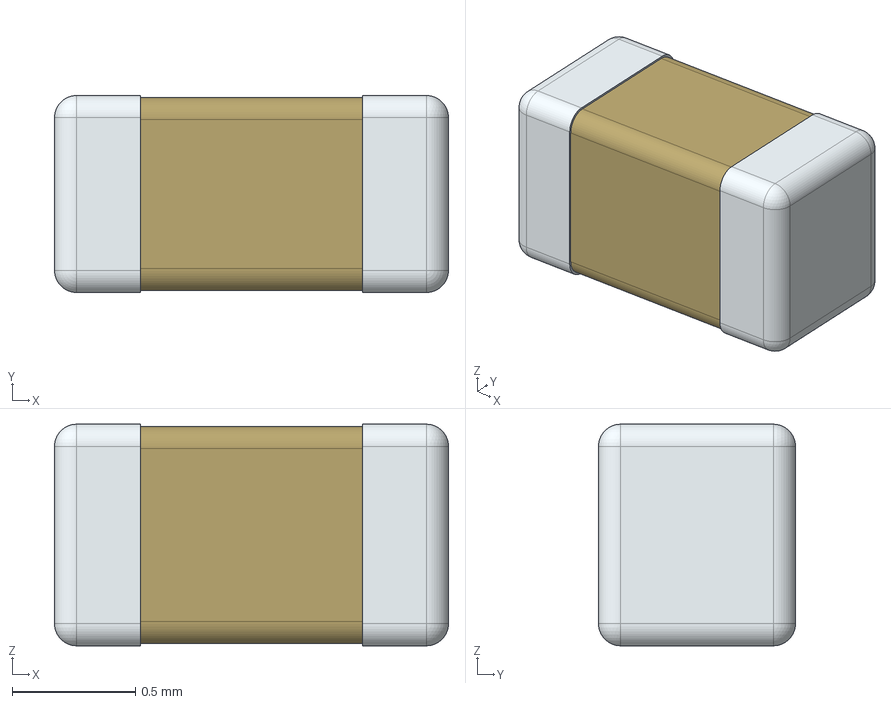
[picture p74: CAD file, 2025-10-18]
04_Hardware/PCBs/CamTracker/KiCad_Libs/Components/LMK107BJ475KA-T/3D/LMK107BJ475KA-T.stp
1.60 x 0.8 x 0.9 mm
