mcihangir/camtracker/04_Hardware/PCBs/CamTracker/KiCad_Libs/Components/LQM2HPN1R0MG0L/3D/LQM2HPN1R0MG0L.stp

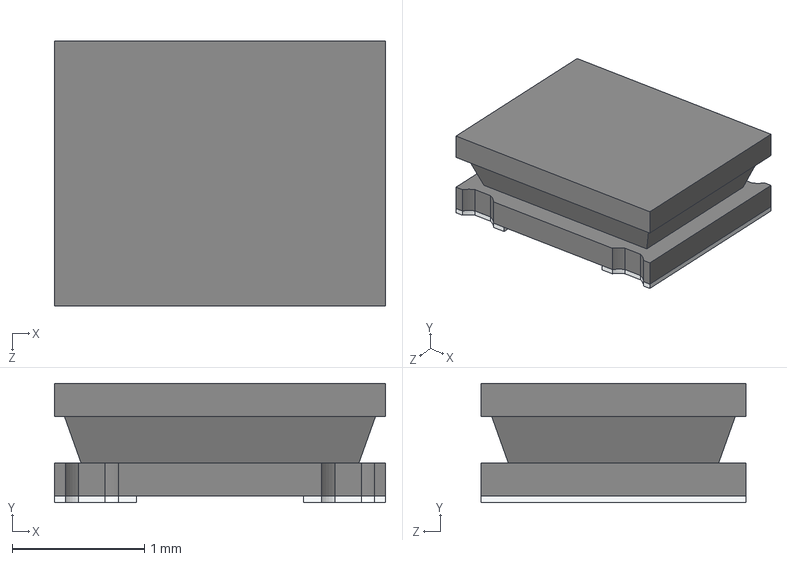
[picture p75: CAD file, 2025-10-18]
04_Hardware/PCBs/CamTracker/KiCad_Libs/Components/LQM2HPN1R0MG0L/3D/LQM2HPN1R0MG0L.stp
2.50 x 0.9 x 2.00 mm
