mcihangir/camtracker/04_Hardware/PCBs/CamTracker/KiCad_Libs/Components/LQW18CNR16J00D/3D/LQW18CNR16J00D.stp

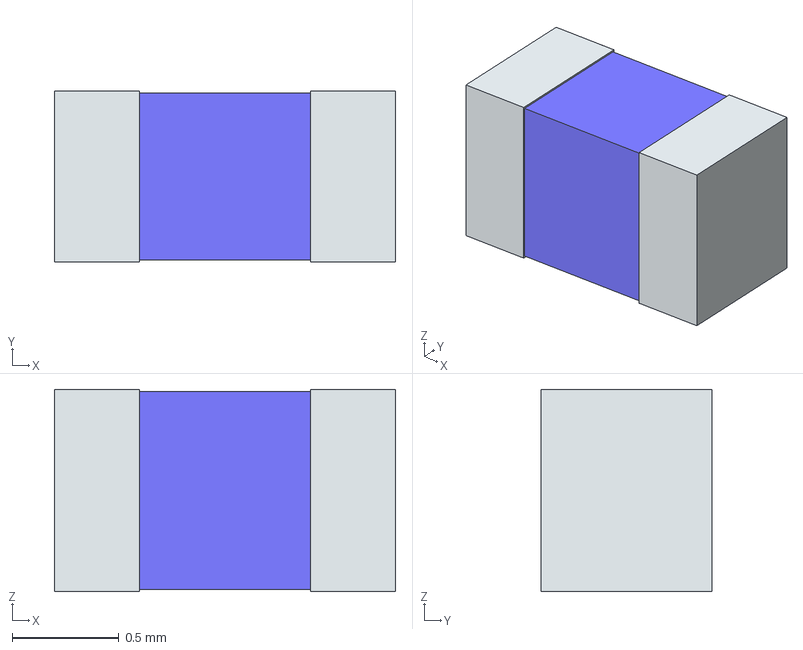
[picture p76: CAD file, 2025-10-18]
04_Hardware/PCBs/CamTracker/KiCad_Libs/Components/LQW18CNR16J00D/3D/LQW18CNR16J00D.stp
1.60 x 0.8 x 0.95 mm
term1
term2
