mcihangir/camtracker/04_Hardware/PCBs/CamTracker/KiCad_Libs/Components/LQW18CNR16J00D/KiCad/LQW18CNR16J00D.step

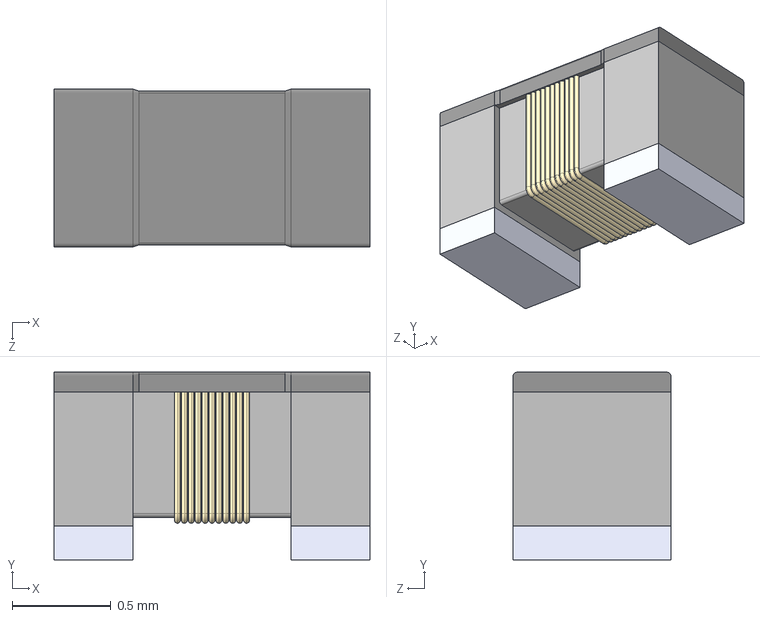
[picture p77: CAD file, 2025-10-18]
04_Hardware/PCBs/CamTracker/KiCad_Libs/Components/LQW18CNR16J00D/KiCad/LQW18CNR16J00D.step
1.60 x 0.95 x 0.8 mm
