mcihangir/camtracker/04_Hardware/PCBs/CamTracker/KiCad_Libs/Components/LTPL_C034UVH405/LED_LTPL-C034UVHXXX_LTO.step

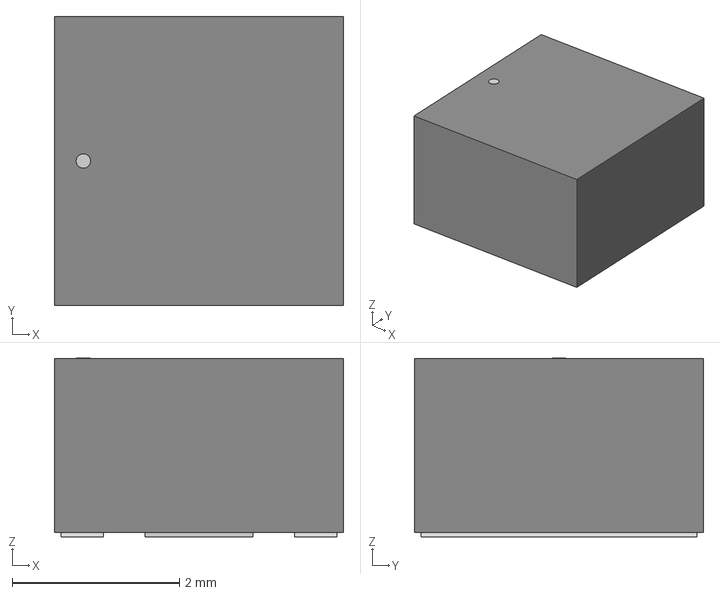
[picture p78: CAD file, 2025-10-18]
04_Hardware/PCBs/CamTracker/KiCad_Libs/Components/LTPL_C034UVH405/LED_LTPL-C034UVHXXX_LTO.step
3.45 x 3.45 x 2.14 mm
