mcihangir/camtracker/04_Hardware/PCBs/CamTracker/KiCad_Libs/Components/LTST-C193KGKT-5A/3D/LTST-C193KGKT-5A.stp

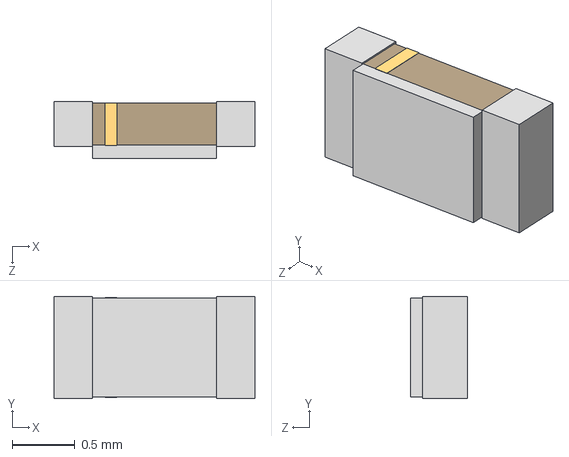
[picture p79: CAD file, 2025-10-18]
04_Hardware/PCBs/CamTracker/KiCad_Libs/Components/LTST-C193KGKT-5A/3D/LTST-C193KGKT-5A.stp
1.60 x 0.812 x 0.45 mm
