mcihangir/camtracker/04_Hardware/PCBs/CamTracker/KiCad_Libs/Components/MEM2067-02-180-00-A/3D/MEM2067-02-180-00-A.stp

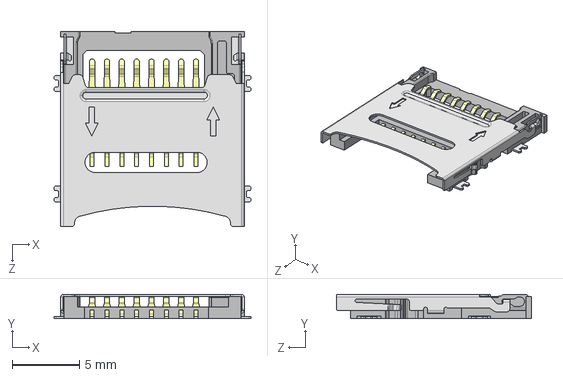
[picture p80: CAD file, 2025-10-18]
04_Hardware/PCBs/CamTracker/KiCad_Libs/Components/MEM2067-02-180-00-A/3D/MEM2067-02-180-00-A.stp
14.6 x 1.80 x 14.4 mm
