mcihangir/camtracker/04_Hardware/PCBs/CamTracker/KiCad_Libs/Components/MMC3630KJ/3D/MMC3630KJ.stp

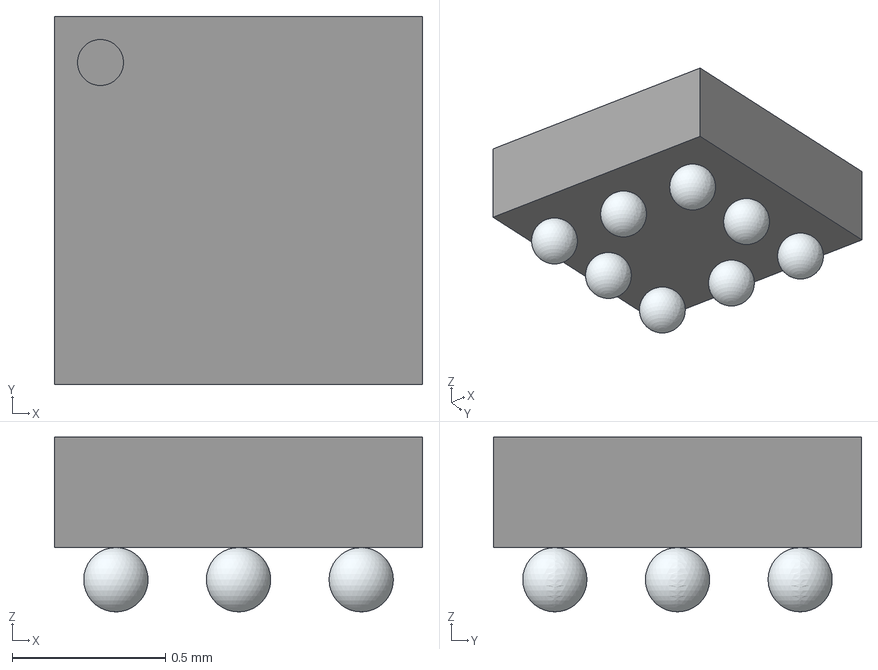
[picture p81: CAD file, 2025-10-18]
04_Hardware/PCBs/CamTracker/KiCad_Libs/Components/MMC3630KJ/3D/MMC3630KJ.stp
1.20 x 1.20 x 0.57 mm
A1
A2
A3
B1
B3
C1
C2
C3
