mcihangir/camtracker/04_Hardware/PCBs/CamTracker/KiCad_Libs/Components/NVME konnektörü/1-2199230-4.stp

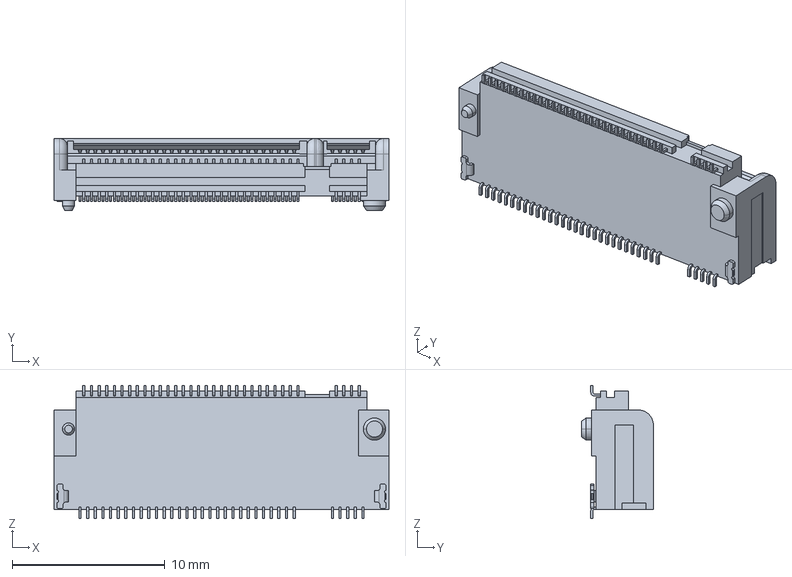
[picture p82: CAD file, 2025-10-18]
04_Hardware/PCBs/CamTracker/KiCad_Libs/Components/NVME konnektörü/1-2199230-4.stp
21.9 x 4.70 x 8.70 mm
