mcihangir/camtracker/04_Hardware/PCBs/CamTracker/KiCad_Libs/Components/nvme_ssd/M.2-2280.step

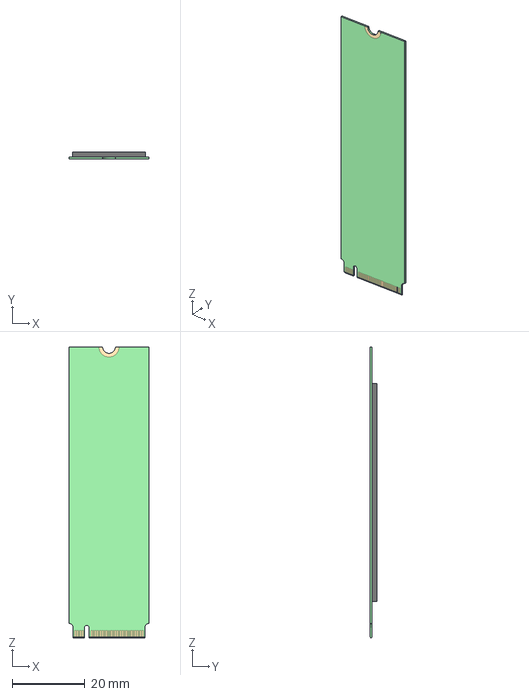
[picture p83: CAD file, 2025-10-29]
04_Hardware/PCBs/CamTracker/KiCad_Libs/Components/nvme_ssd/M.2-2280.step
22.0 x 1.86 x 80.0 mm
