mcihangir/camtracker/04_Hardware/PCBs/CamTracker/KiCad_Libs/Components/OC2321VQFN8XTMA1_kicad/PG-VQFN-8-4.STEP

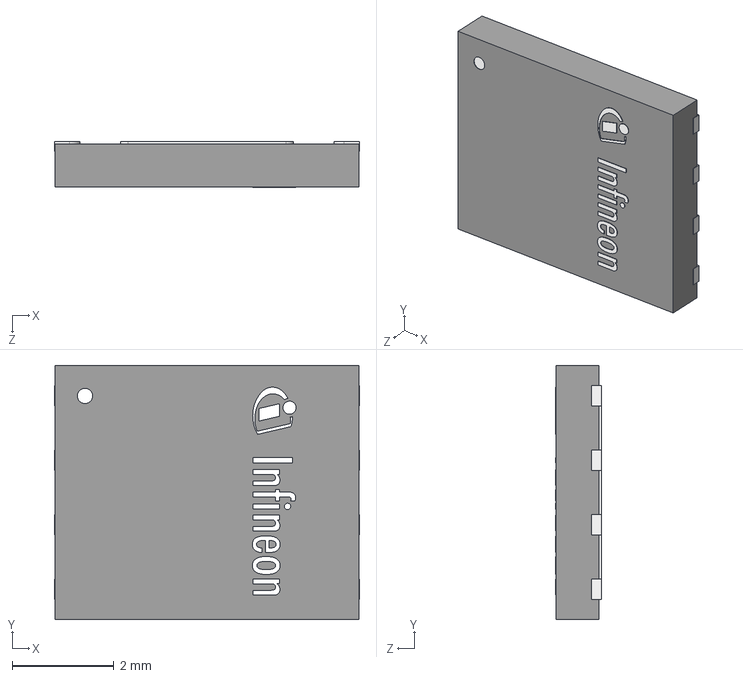
[picture p84: CAD file, 2025-10-18]
04_Hardware/PCBs/CamTracker/KiCad_Libs/Components/OC2321VQFN8XTMA1_kicad/PG-VQFN-8-4.STEP
6.00 x 5.00 x 0.91 mm
