mcihangir/camtracker/04_Hardware/PCBs/CamTracker/KiCad_Libs/Components/PAM8302AASCR/3D/PAM8302AASCR.stp

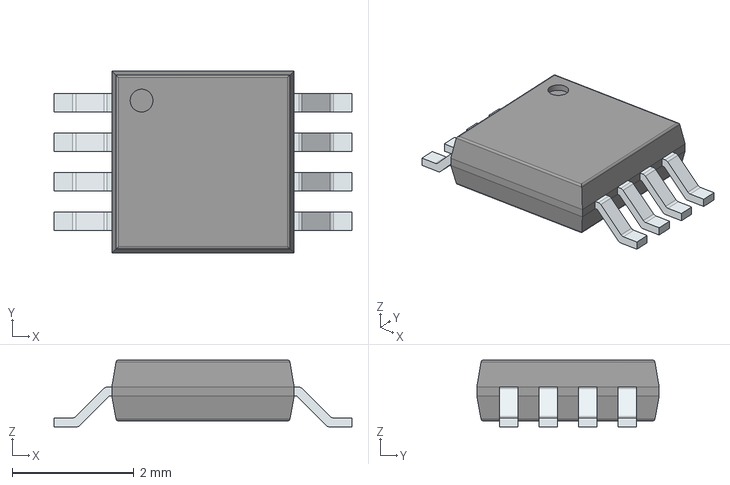
[picture p85: CAD file, 2025-10-18]
04_Hardware/PCBs/CamTracker/KiCad_Libs/Components/PAM8302AASCR/3D/PAM8302AASCR.stp
4.90 x 3.00 x 1.10 mm
PinsArrayLR
