mcihangir/camtracker/04_Hardware/PCBs/CamTracker/KiCad_Libs/Components/PCA9306DCTT/3D/PCA9306DCTT.stp

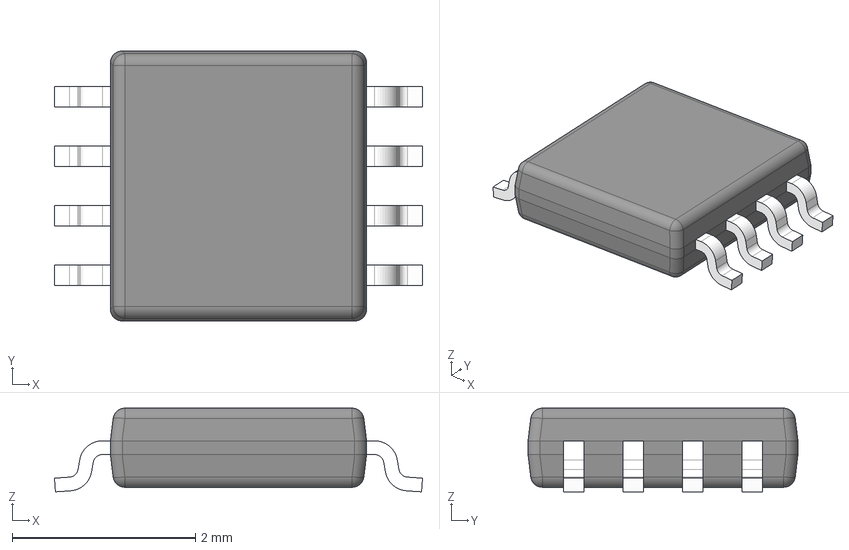
[picture p86: CAD file, 2025-10-18]
04_Hardware/PCBs/CamTracker/KiCad_Libs/Components/PCA9306DCTT/3D/PCA9306DCTT.stp
4.02 x 2.95 x 0.915 mm
BODY-SO
LEAD-SO x 8
PIN1-ID
