mcihangir/camtracker/04_Hardware/PCBs/CamTracker/KiCad_Libs/Components/PESD3V3L5UF,115/3D/PESD3V3L5UF,115.stp

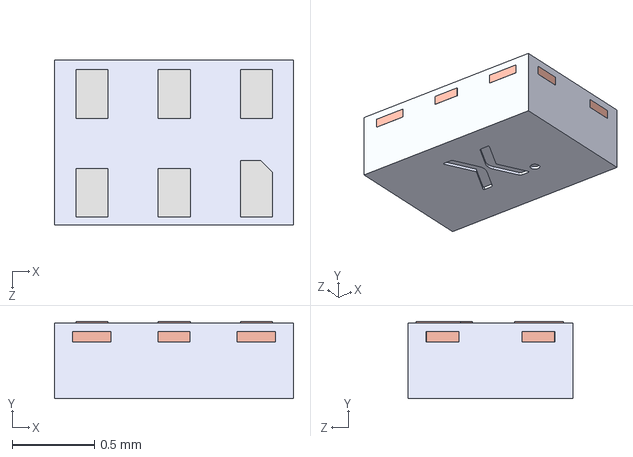
[picture p87: CAD file, 2025-10-18]
04_Hardware/PCBs/CamTracker/KiCad_Libs/Components/PESD3V3L5UF,115/3D/PESD3V3L5UF,115.stp
1.45 x 0.47 x 1.00 mm
SOT886 LF
SOT886 Mold Body
