mcihangir/camtracker/04_Hardware/PCBs/CamTracker/KiCad_Libs/Components/PJ-059A/3D/PJ-059A.stp

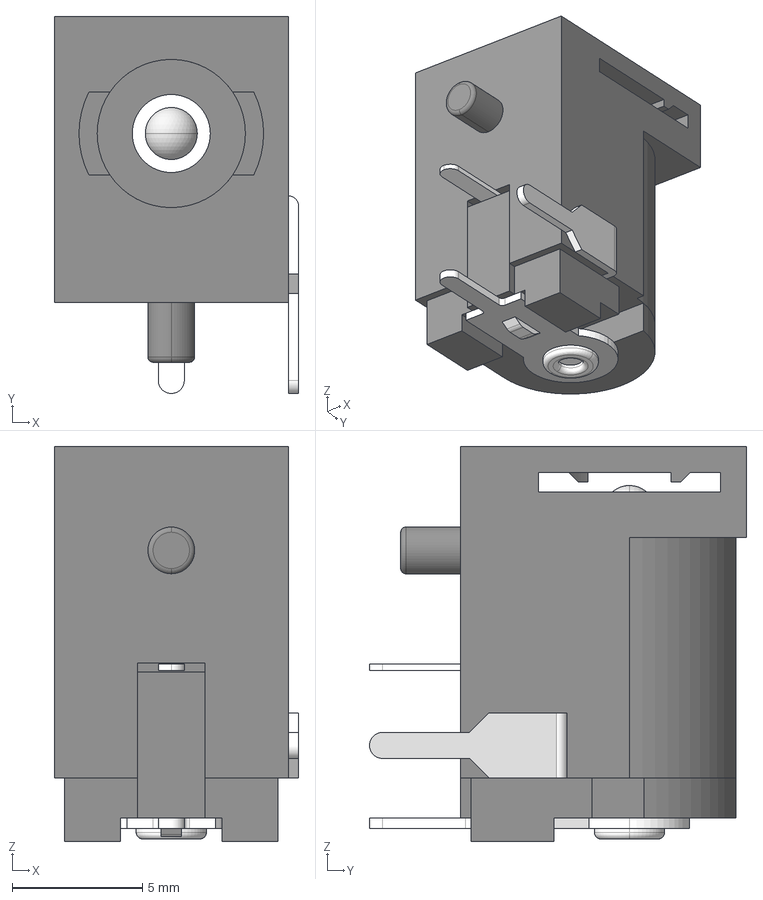
[picture p88: CAD file, 2025-10-18]
04_Hardware/PCBs/CamTracker/KiCad_Libs/Components/PJ-059A/3D/PJ-059A.stp
9.40 x 14.5 x 15.2 mm
