mcihangir/camtracker/04_Hardware/PCBs/CamTracker/KiCad_Libs/Components/PN7220/PN7221EV/3D/PN7221EV.stp

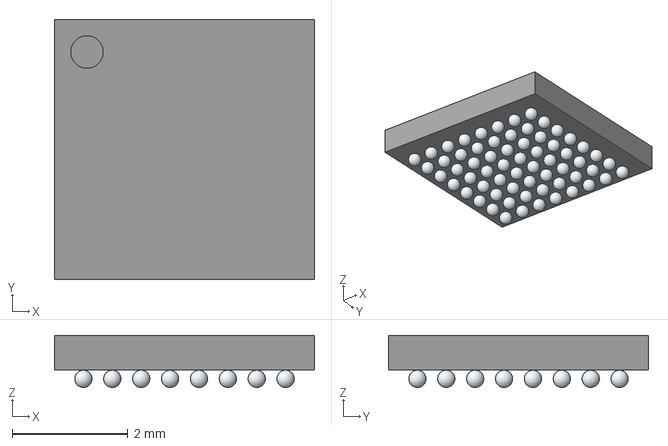
[picture p89: CAD file, 2025-10-18]
04_Hardware/PCBs/CamTracker/KiCad_Libs/Components/PN7220/PN7221EV/3D/PN7221EV.stp
4.50 x 4.50 x 0.9 mm
