mcihangir/camtracker/04_Hardware/PCBs/CamTracker/KiCad_Libs/Components/RB751S40/RB751S40,115.stp

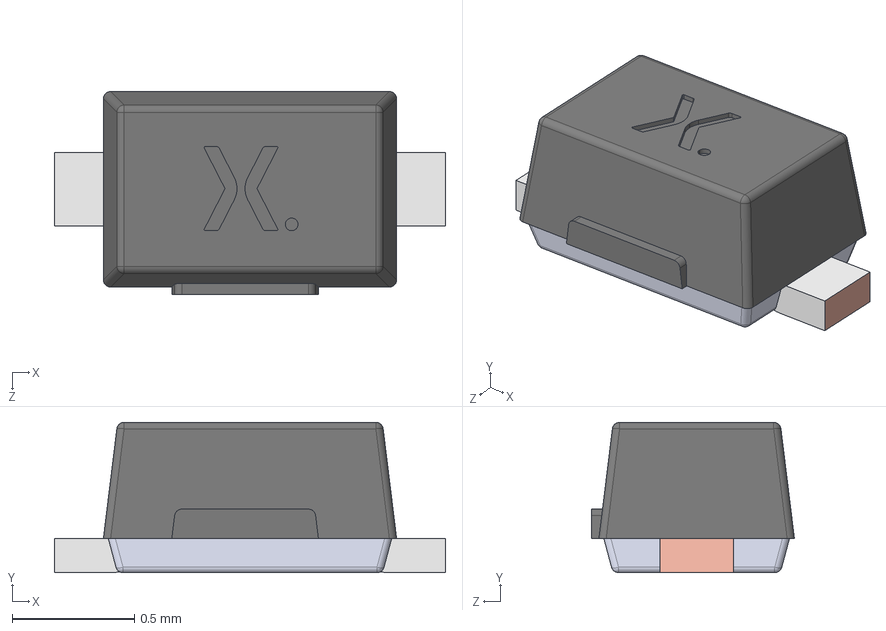
[picture p90: CAD file, 2025-10-18]
04_Hardware/PCBs/CamTracker/KiCad_Libs/Components/RB751S40/RB751S40,115.stp
1.60 x 0.615 x 0.83 mm
SOD523 Lead
SOD523 Lower body
SOD523 Upper body
