mcihangir/camtracker/04_Hardware/PCBs/CamTracker/KiCad_Libs/Components/RL1220T-R020-J/RL1220T-R020-J.step

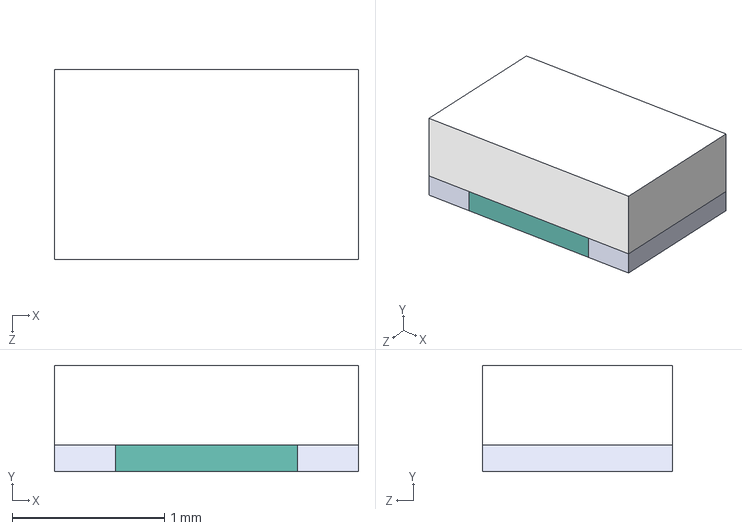
[picture p91: CAD file, 2025-10-18]
04_Hardware/PCBs/CamTracker/KiCad_Libs/Components/RL1220T-R020-J/RL1220T-R020-J.step
2.00 x 0.7 x 1.25 mm
