mcihangir/camtracker/04_Hardware/PCBs/CamTracker/KiCad_Libs/Components/RT8279GSP/3D/RT8279GSP.stp

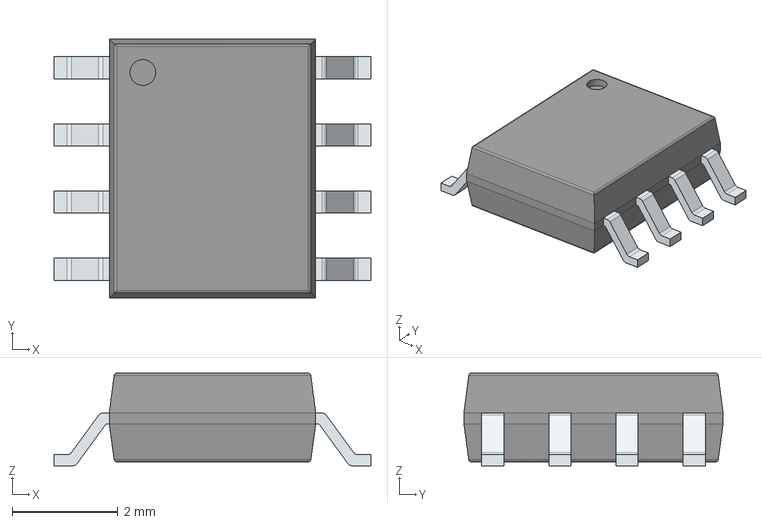
[picture p92: CAD file, 2025-10-18]
04_Hardware/PCBs/CamTracker/KiCad_Libs/Components/RT8279GSP/3D/RT8279GSP.stp
6.00 x 4.90 x 1.75 mm
PinsArrayLR
