mcihangir/camtracker/04_Hardware/PCBs/CamTracker/KiCad_Libs/Components/RT8279GSP/KiCad/SOP8L_EP1_RIT.step

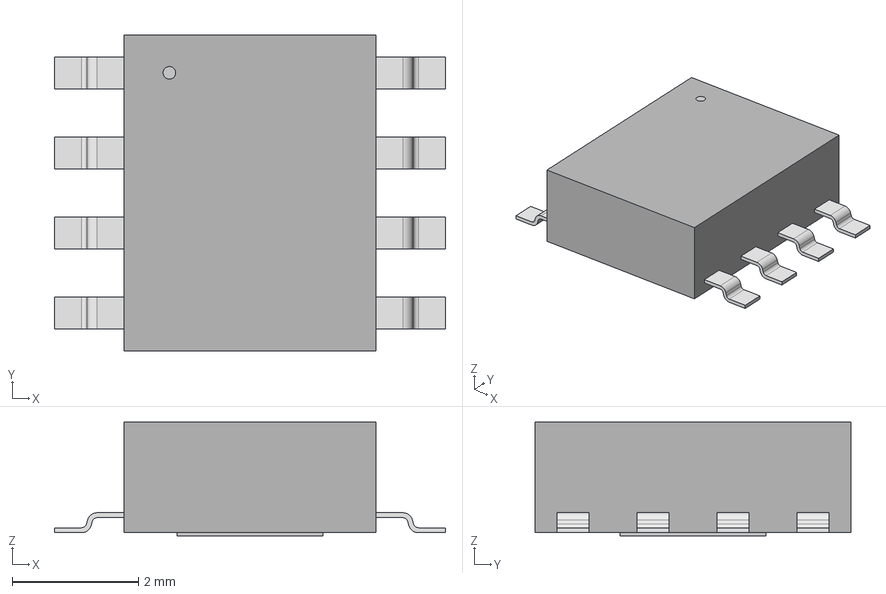
[picture p93: CAD file, 2025-10-18]
04_Hardware/PCBs/CamTracker/KiCad_Libs/Components/RT8279GSP/KiCad/SOP8L_EP1_RIT.step
6.20 x 5.00 x 1.81 mm
