mcihangir/camtracker/04_Hardware/PCBs/CamTracker/KiCad_Libs/Components/SC1105-01UTG/3D/SC1105-01UTG.stp

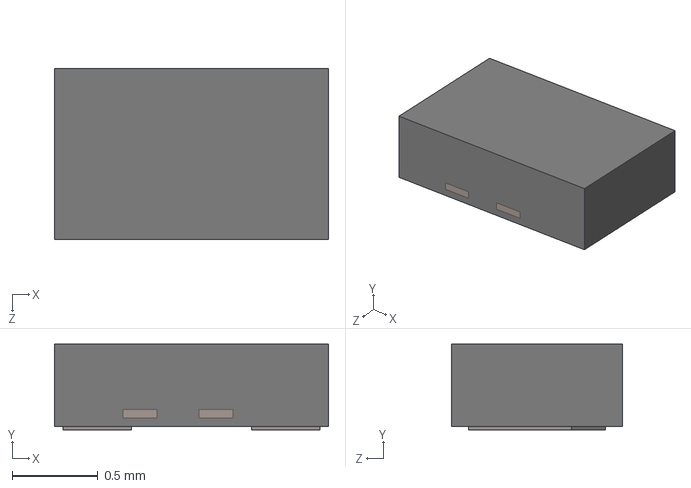
[picture p94: CAD file, 2025-10-18]
04_Hardware/PCBs/CamTracker/KiCad_Libs/Components/SC1105-01UTG/3D/SC1105-01UTG.stp
1.60 x 0.5 x 1.00 mm
