mcihangir/camtracker/04_Hardware/PCBs/CamTracker/KiCad_Libs/Components/SC1205-01ETG/3D/SC1205-01ETG.stp

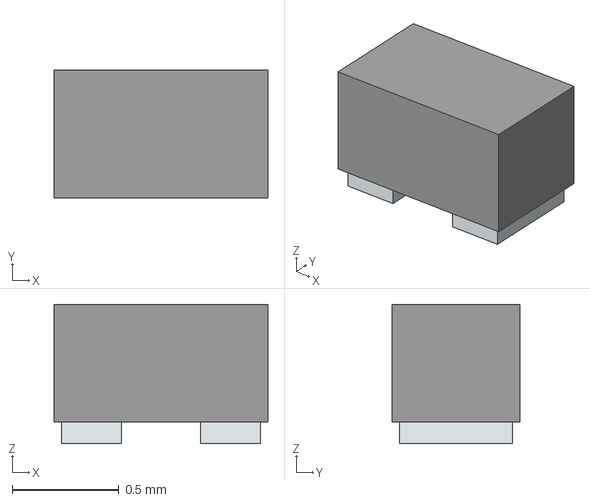
[picture p95: CAD file, 2025-10-18]
04_Hardware/PCBs/CamTracker/KiCad_Libs/Components/SC1205-01ETG/3D/SC1205-01ETG.stp
1.00 x 0.6 x 0.65 mm
Pins
