mcihangir/camtracker/04_Hardware/PCBs/CamTracker/KiCad_Libs/Components/SD12C.TCT/3D/SD12C.TCT.stp

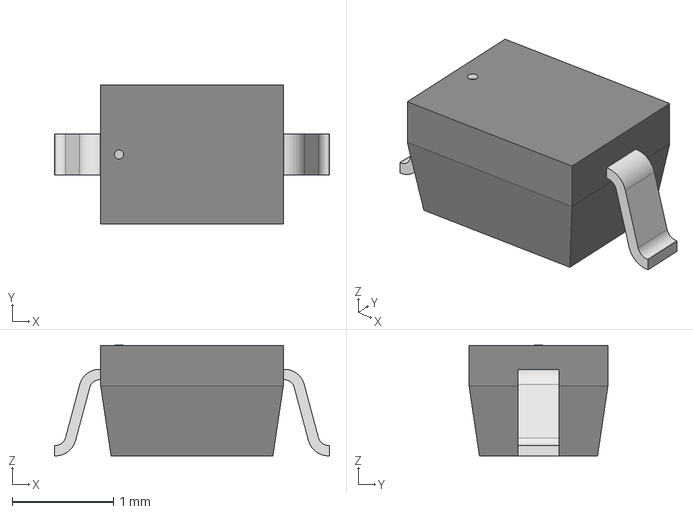
[picture p96: CAD file, 2025-10-18]
04_Hardware/PCBs/CamTracker/KiCad_Libs/Components/SD12C.TCT/3D/SD12C.TCT.stp
2.72 x 1.37 x 1.09 mm
