mcihangir/camtracker/04_Hardware/PCBs/CamTracker/KiCad_Libs/Components/SGM804/SOT23-5.step

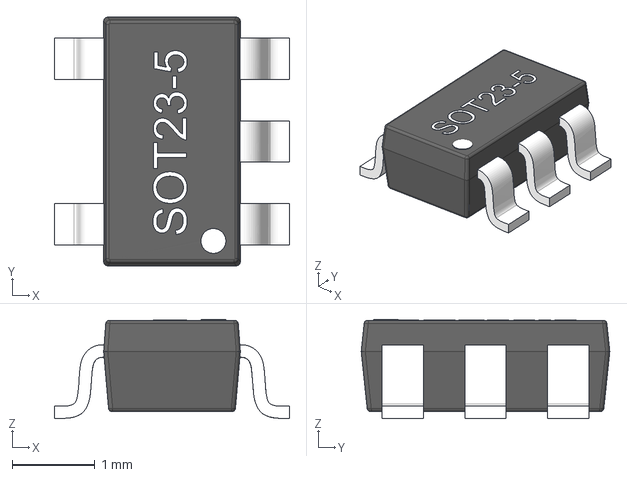
[picture p97: CAD file, 2025-10-29]
04_Hardware/PCBs/CamTracker/KiCad_Libs/Components/SGM804/SOT23-5.step
2.84 x 3.00 x 1.20 mm
