mcihangir/camtracker/04_Hardware/PCBs/CamTracker/KiCad_Libs/Components/SHOU HAN 1.25-15P LT/JST - GH - SMD (R) - 15Pin - 1.25mm.stp

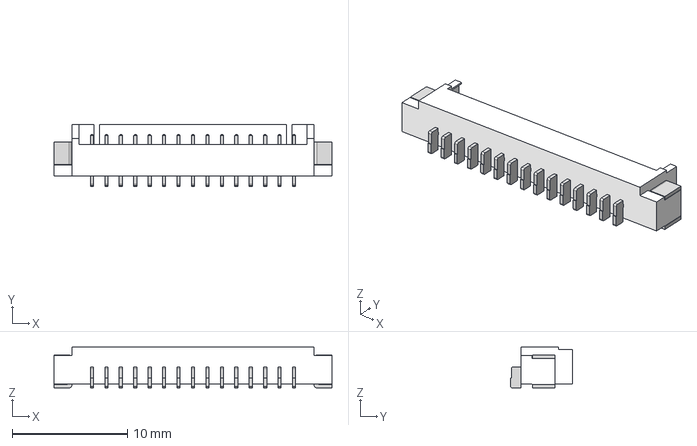
[picture p98: CAD file, 2025-10-18]
04_Hardware/PCBs/CamTracker/KiCad_Libs/Components/SHOU HAN 1.25-15P LT/JST - GH - SMD (R) - 15Pin - 1.25mm.stp
24.1 x 5.35 x 3.53 mm
