mcihangir/camtracker/04_Hardware/PCBs/CamTracker/KiCad_Libs/Components/SHOU HAN 1.25-4P LT/JST - GH - SMD (R) - 4Pin - 1.25mm.stp

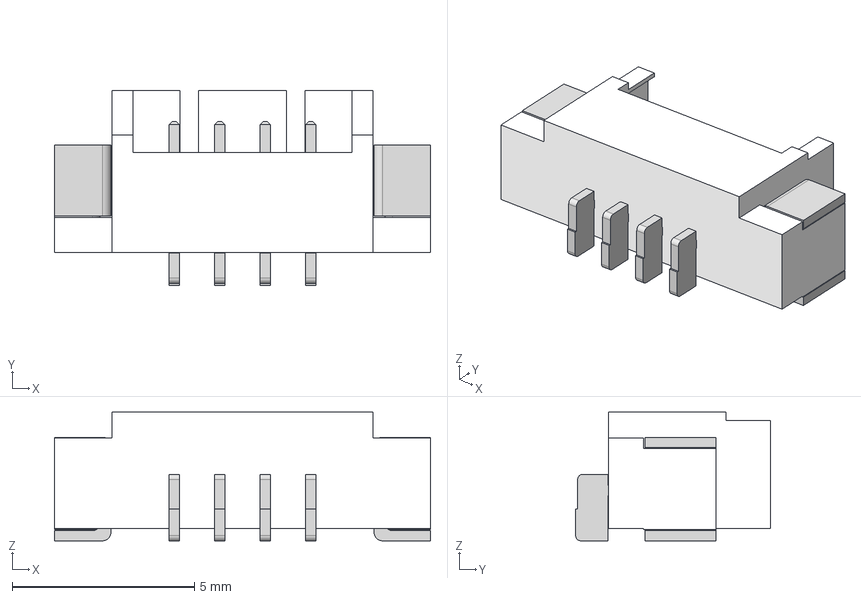
[picture p99: CAD file, 2025-10-18]
04_Hardware/PCBs/CamTracker/KiCad_Libs/Components/SHOU HAN 1.25-4P LT/JST - GH - SMD (R) - 4Pin - 1.25mm.stp
10.3 x 5.35 x 3.53 mm
