mcihangir/camtracker/04_Hardware/PCBs/CamTracker/KiCad_Libs/Components/SML-P11VTT86R/3D/SML-P11VTT86R.stp

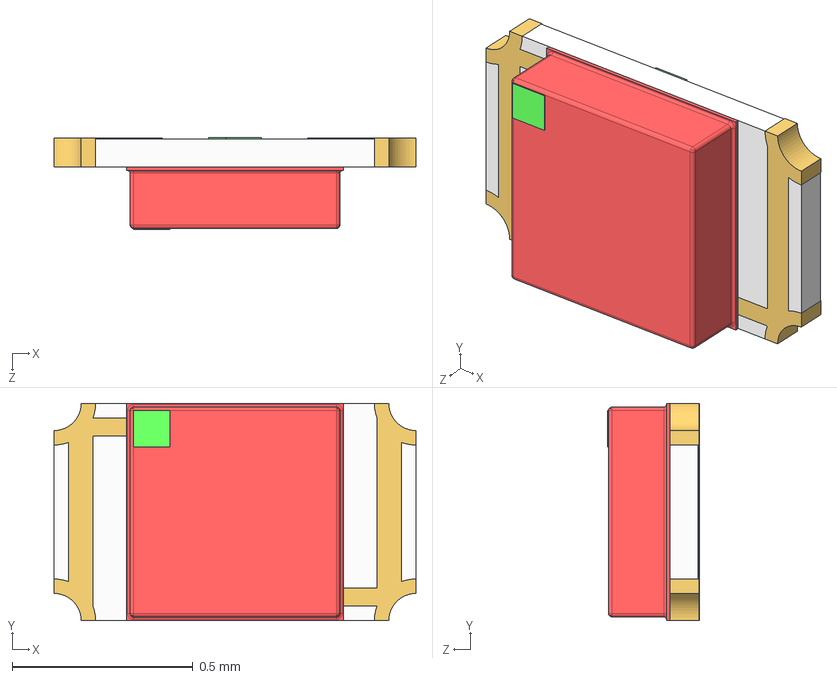
[picture p100: CAD file, 2025-10-18]
04_Hardware/PCBs/CamTracker/KiCad_Libs/Components/SML-P11VTT86R/3D/SML-P11VTT86R.stp
1.00 x 0.6 x 0.255 mm
terminals_2
terminals
lens
cathod mark
cathod mark_2
