mcihangir/camtracker/04_Hardware/PCBs/CamTracker/KiCad_Libs/Components/SP0402U-ULC-02ETG/3D/SP0402U-ULC-02ETG.stp

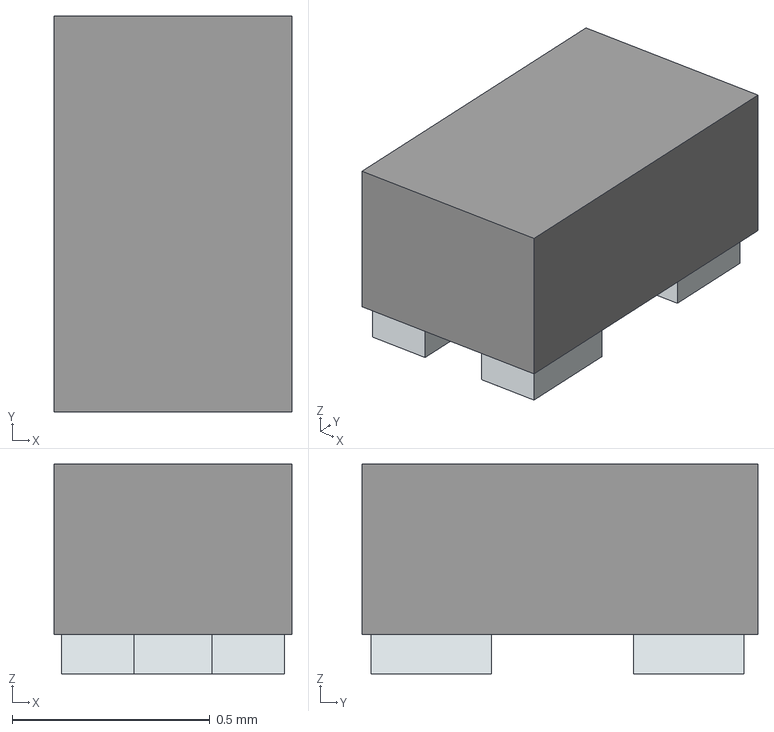
[picture p101: CAD file, 2025-10-18]
04_Hardware/PCBs/CamTracker/KiCad_Libs/Components/SP0402U-ULC-02ETG/3D/SP0402U-ULC-02ETG.stp
0.6 x 1.00 x 0.53 mm
Pins
