mcihangir/camtracker/04_Hardware/PCBs/CamTracker/KiCad_Libs/Components/SRV05-4.TCT/3D/SRV05-4.TCT.stp

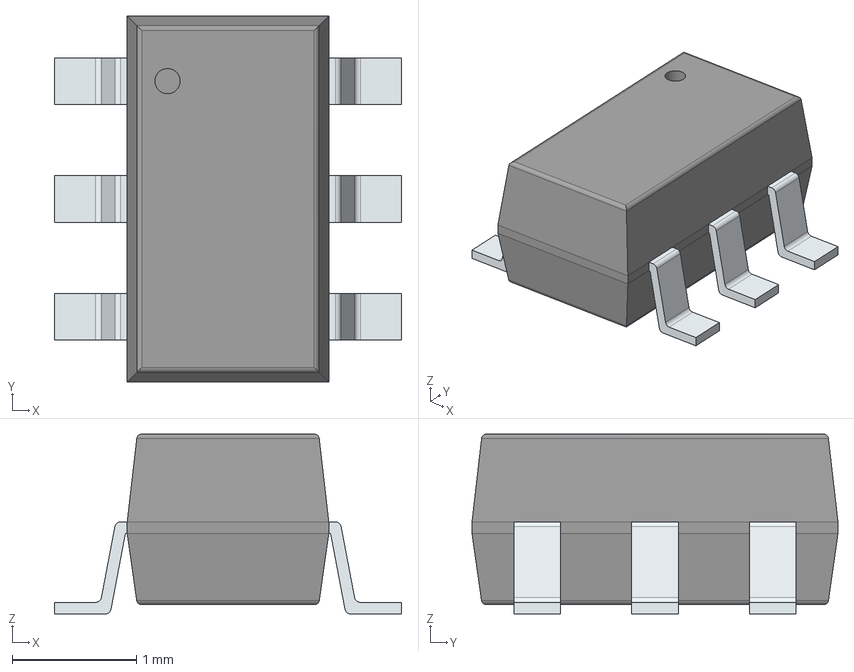
[picture p102: CAD file, 2025-10-18]
04_Hardware/PCBs/CamTracker/KiCad_Libs/Components/SRV05-4.TCT/3D/SRV05-4.TCT.stp
2.80 x 2.95 x 1.45 mm
PinsArrayLR
