mcihangir/camtracker/04_Hardware/PCBs/CamTracker/KiCad_Libs/Components/ST4SI2M0020TPIFW/3D/ST4SI2M0020TPIFW.stp

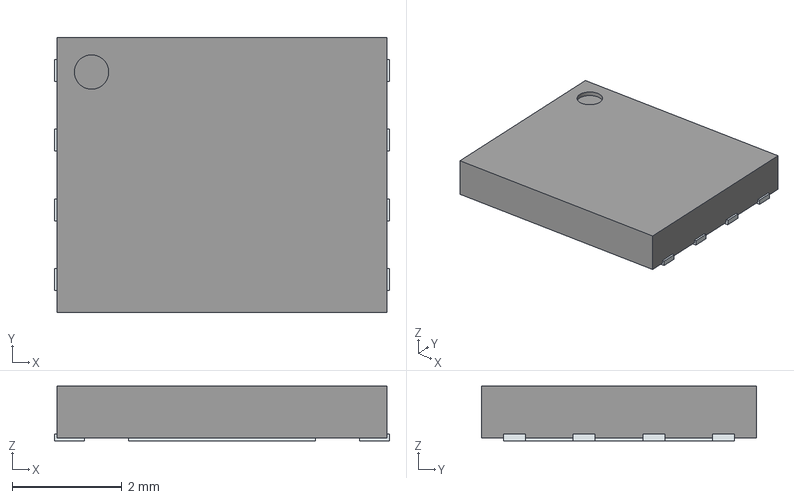
[picture p103: CAD file, 2025-10-18]
04_Hardware/PCBs/CamTracker/KiCad_Libs/Components/ST4SI2M0020TPIFW/3D/ST4SI2M0020TPIFW.stp
6.10 x 5.00 x 1.00 mm
ThermalPin
PinsArrayLR
