mcihangir/camtracker/04_Hardware/PCBs/CamTracker/KiCad_Libs/Components/T495D107K010ATE080/3D/T495D107K010ATE080.stp

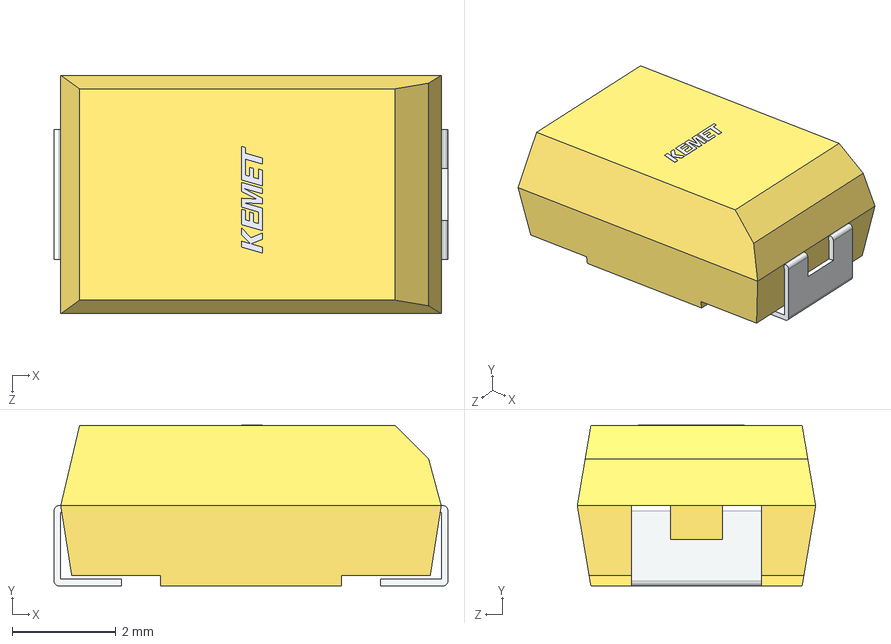
[picture p104: CAD file, 2025-10-18]
04_Hardware/PCBs/CamTracker/KiCad_Libs/Components/T495D107K010ATE080/3D/T495D107K010ATE080.stp
7.60 x 3.11 x 4.60 mm
