mcihangir/camtracker/04_Hardware/PCBs/CamTracker/KiCad_Libs/Components/T495X107M016ATE1007280/3D/T495X107M016ATE1007280.stp

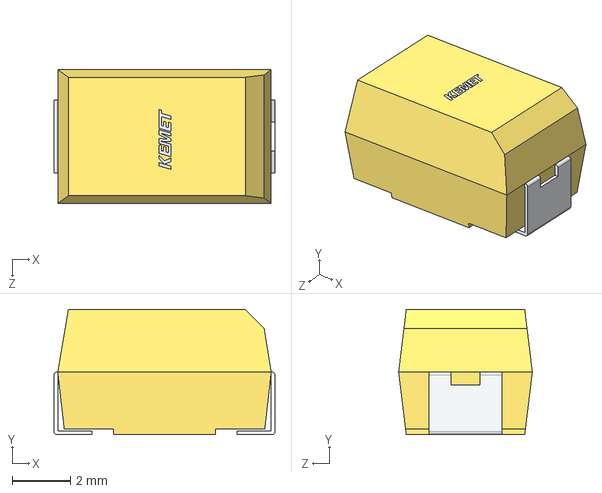
[picture p105: CAD file, 2025-10-18]
04_Hardware/PCBs/CamTracker/KiCad_Libs/Components/T495X107M016ATE1007280/3D/T495X107M016ATE1007280.stp
7.60 x 4.31 x 4.60 mm
