mcihangir/camtracker/04_Hardware/PCBs/CamTracker/KiCad_Libs/Components/TAJB107M006RNJ/3D/TAJB107M006RNJ.stp

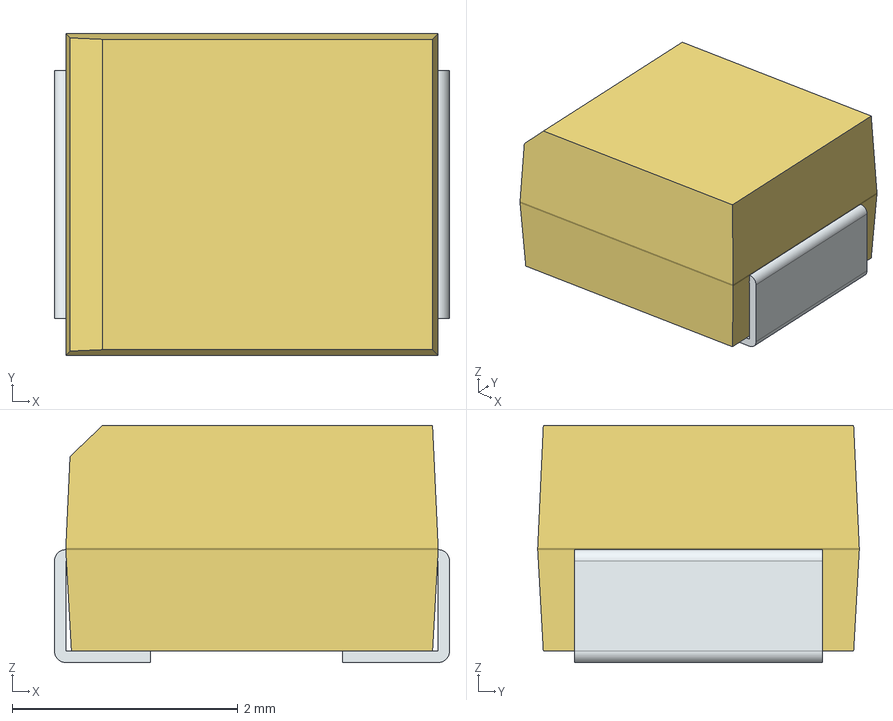
[picture p106: CAD file, 2025-10-18]
04_Hardware/PCBs/CamTracker/KiCad_Libs/Components/TAJB107M006RNJ/3D/TAJB107M006RNJ.stp
3.50 x 2.85 x 2.10 mm
FilletPin1
FilletPin2
