mcihangir/camtracker/04_Hardware/PCBs/CamTracker/KiCad_Libs/Components/TE_Connectivity/2201778_1/c-2201778-1-a-3d.stp

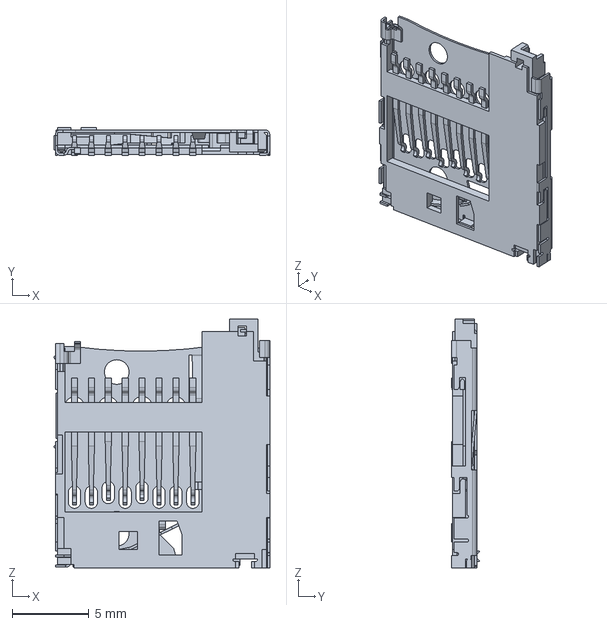
[picture p107: CAD file, 2025-12-15]
04_Hardware/PCBs/CamTracker/KiCad_Libs/Components/TE_Connectivity/2201778_1/c-2201778-1-a-3d.stp
14.0 x 1.80 x 16.2 mm
