mcihangir/camtracker/04_Hardware/PCBs/CamTracker/KiCad_Libs/Components/TXS0102DCUR/3D/TXS0102DCUR.stp

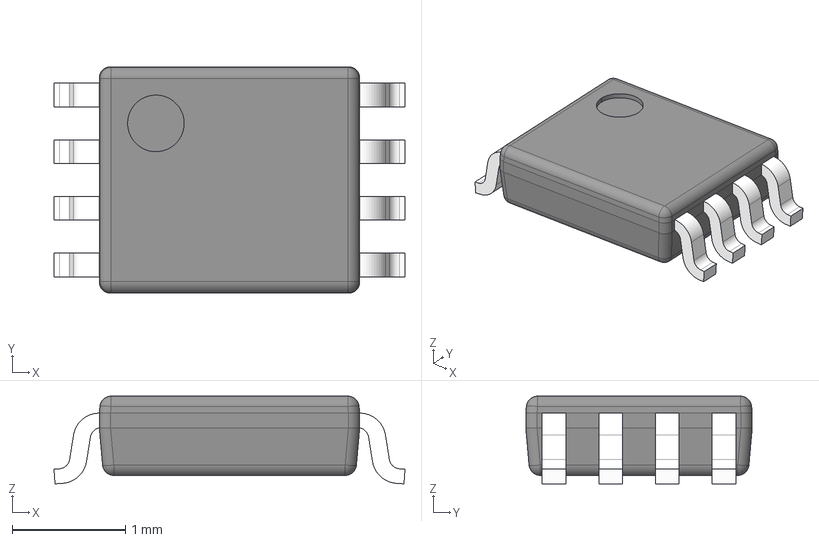
[picture p108: CAD file, 2025-10-18]
04_Hardware/PCBs/CamTracker/KiCad_Libs/Components/TXS0102DCUR/3D/TXS0102DCUR.stp
3.10 x 2.00 x 0.775 mm
BODY-VSSOP
LEAD-VSSOP x 8
