mcihangir/camtracker/04_Hardware/PCBs/CamTracker/KiCad_Libs/Components/ul_74404024010/IND_WE-LQS_2512_WRE.step

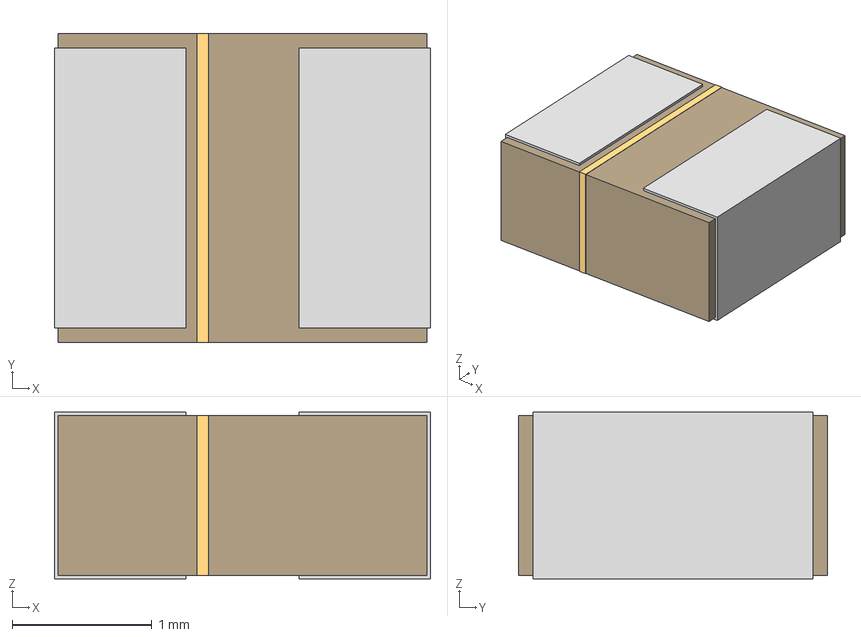
[picture p109: CAD file, 2025-10-18]
04_Hardware/PCBs/CamTracker/KiCad_Libs/Components/ul_74404024010/IND_WE-LQS_2512_WRE.step
2.69 x 2.21 x 1.19 mm
