mcihangir/camtracker/04_Hardware/PCBs/CamTracker/KiCad_Libs/Components/ul_CL10C390FB81PNC/CAP_CL10_SAM.step

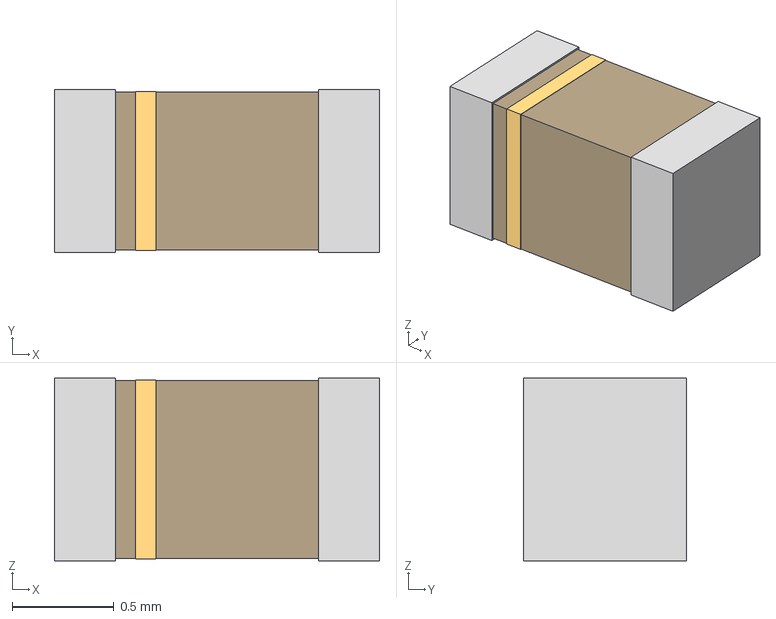
[picture p110: CAD file, 2025-10-18]
04_Hardware/PCBs/CamTracker/KiCad_Libs/Components/ul_CL10C390FB81PNC/CAP_CL10_SAM.step
1.60 x 0.8 x 0.9 mm
