mcihangir/camtracker/04_Hardware/PCBs/CamTracker/KiCad_Libs/Components/ul_RC0402JR-070RL/RC0402N_YAG.step

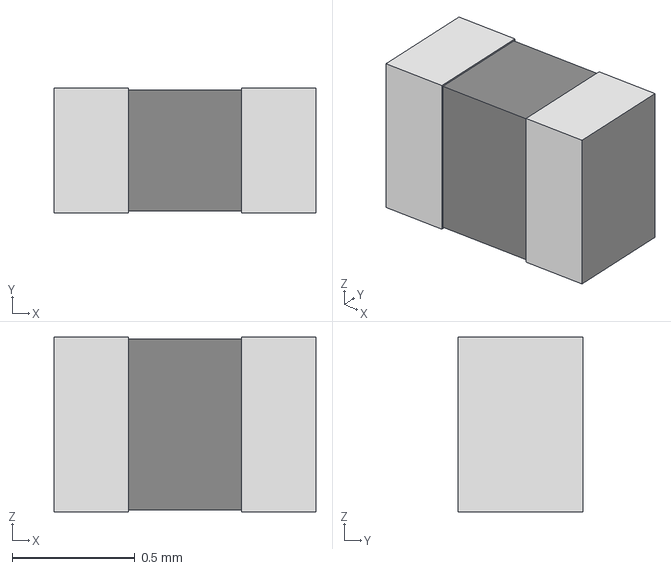
[picture p111: CAD file, 2025-10-18]
04_Hardware/PCBs/CamTracker/KiCad_Libs/Components/ul_RC0402JR-070RL/RC0402N_YAG.step
1.07 x 0.508 x 0.711 mm
