mcihangir/camtracker/04_Hardware/PCBs/CamTracker/KiCad_Libs/Components/ul_UMK325BJ475MM-T/CAP_UMK325B7475MM-T_TAY.step

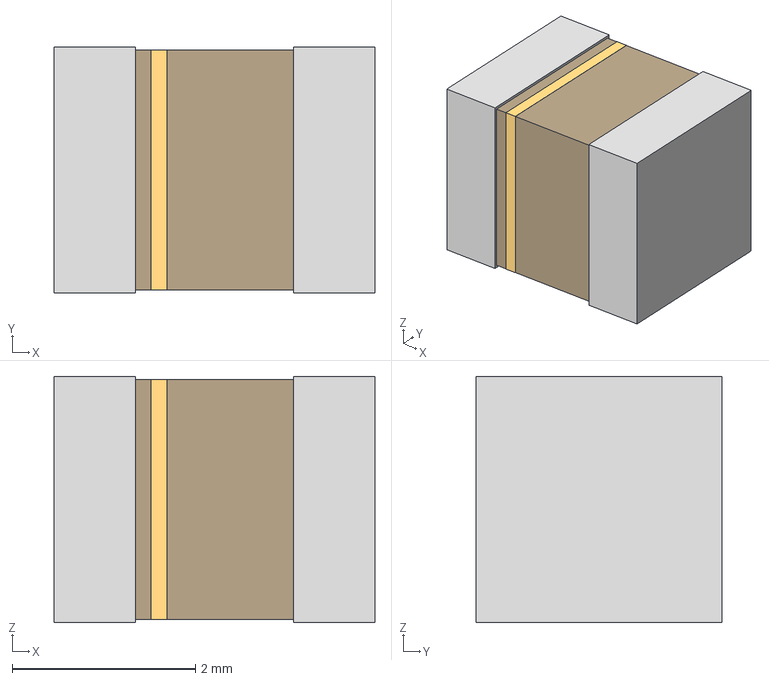
[picture p112: CAD file, 2025-10-18]
04_Hardware/PCBs/CamTracker/KiCad_Libs/Components/ul_UMK325BJ475MM-T/CAP_UMK325B7475MM-T_TAY.step
3.51 x 2.69 x 2.69 mm
