mcihangir/camtracker/04_Hardware/PCBs/CamTracker/KiCad_Libs/Components/USB4080-03-A/USB4080-03-A.stp

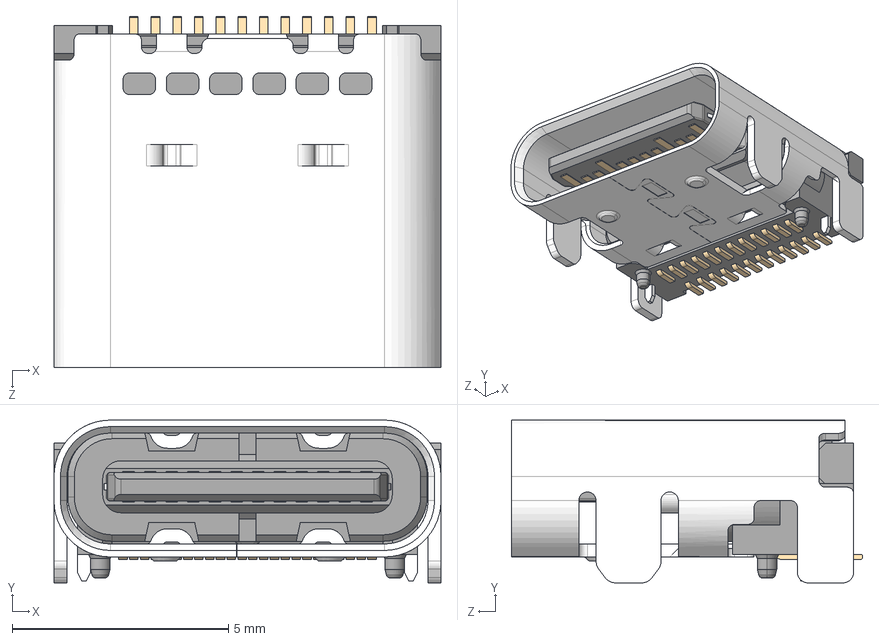
[picture p113: CAD file, 2025-10-18]
04_Hardware/PCBs/CamTracker/KiCad_Libs/Components/USB4080-03-A/USB4080-03-A.stp
8.94 x 3.76 x 8.10 mm
USB4080-03-A_PART3
USB4080-03-A_PART2
USB4080-03-A_PART1
