mcihangir/camtracker/04_Hardware/PCBs/CamTracker/KiCad_Libs/Components/WSL2010R0200FEA/3D/WSL2010R0200FEA.stp

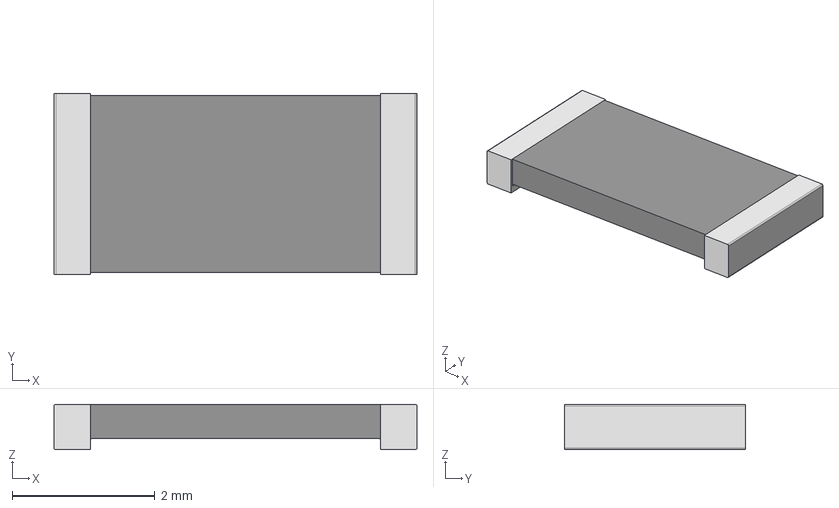
[picture p114: CAD file, 2025-10-18]
04_Hardware/PCBs/CamTracker/KiCad_Libs/Components/WSL2010R0200FEA/3D/WSL2010R0200FEA.stp
5.08 x 2.54 x 0.635 mm
