mcihangir/camtracker/04_Hardware/PCBs/CamTracker/KiCad_Libs/Components/ZF5S-40-01-T-WT/ZF5S-40-01-T-WT.step

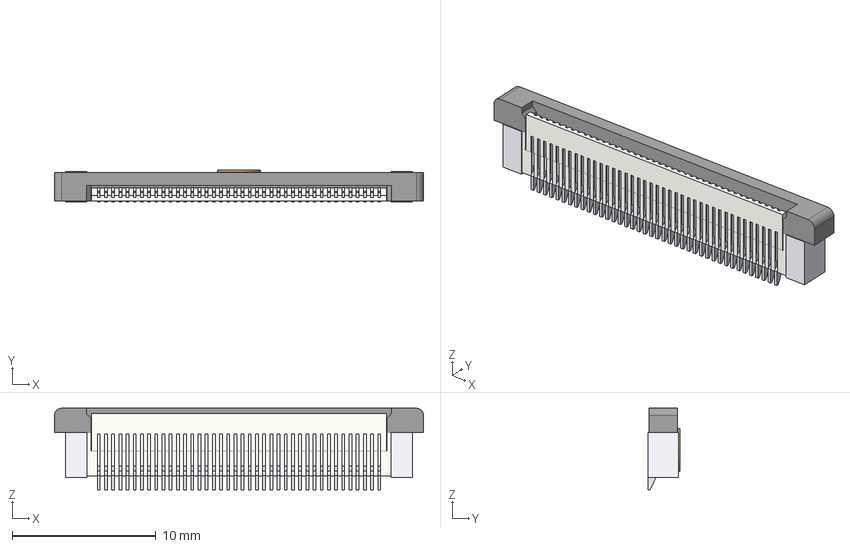
[picture p115: CAD file, 2025-10-18]
04_Hardware/PCBs/CamTracker/KiCad_Libs/Components/ZF5S-40-01-T-WT/ZF5S-40-01-T-WT.step
25.6 x 2.21 x 5.67 mm
ZF5S-40-01-WT_socket
C-297-40-01_pins
K-DOT-.118-.219-.005_polyamide_pick
