mcihangir/camtracker/04_Hardware/PCBs/CamTracker/KiCad_Libs/Components/FH19SC-30S-0.5SH_09_/3D/FH19SC-30S-0.5SH-09---3DModel-STEP-1.STEP

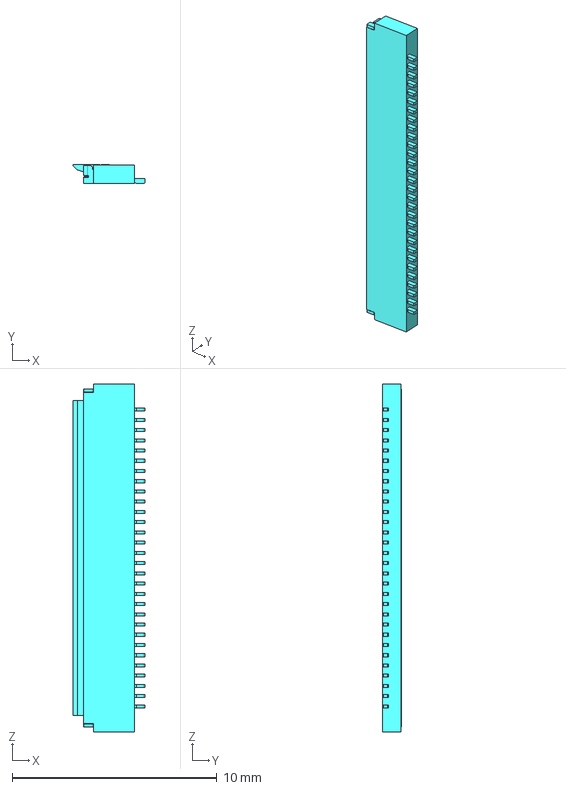
[picture p116: CAD file, 2025-10-18]
04_Hardware/PCBs/CamTracker/KiCad_Libs/Components/FH19SC-30S-0.5SH_09_/3D/FH19SC-30S-0.5SH-09---3DModel-STEP-1.STEP
3.50 x 0.93 x 17.0 mm
