mcihangir/camtracker/04_Hardware/PCBs/CamTracker/KiCad_Libs/Components/FH35C-27S-0.3SHW_50_/3D/FH35C-27S-0.3SHW_50_.stp

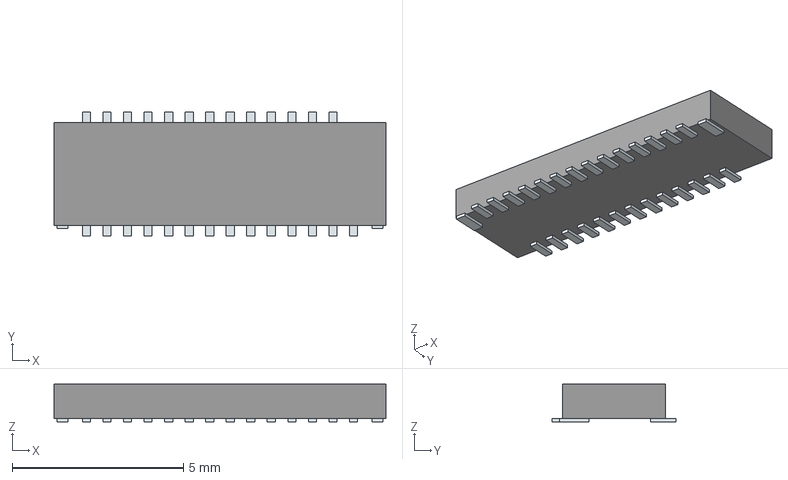
[picture p117: CAD file, 2025-10-18]
04_Hardware/PCBs/CamTracker/KiCad_Libs/Components/FH35C-27S-0.3SHW_50_/3D/FH35C-27S-0.3SHW_50_.stp
9.70 x 3.62 x 1.10 mm
Pins
