mcihangir/camtracker/04_Hardware/PCBs/CamTracker/KiCad_Libs/Components/LTPL_C034UVH405/LTST-C170KRKT.STEP

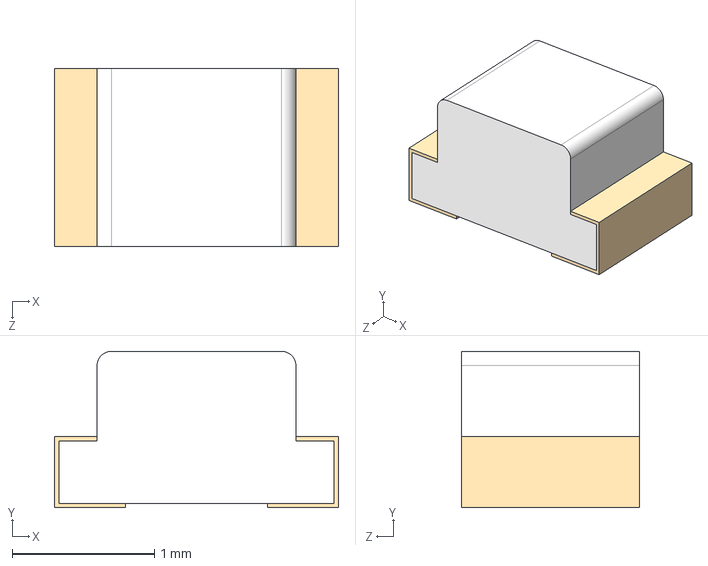
[picture p118: CAD file, 2025-10-18]
04_Hardware/PCBs/CamTracker/KiCad_Libs/Components/LTPL_C034UVH405/LTST-C170KRKT.STEP
2.00 x 1.10 x 1.25 mm
