mcihangir/camtracker/04_Hardware/PCBs/CamTracker/KiCad_Libs/Components/SHOU HAN 1.25-15P LT/SHOUHAN_1x15-Shape.step

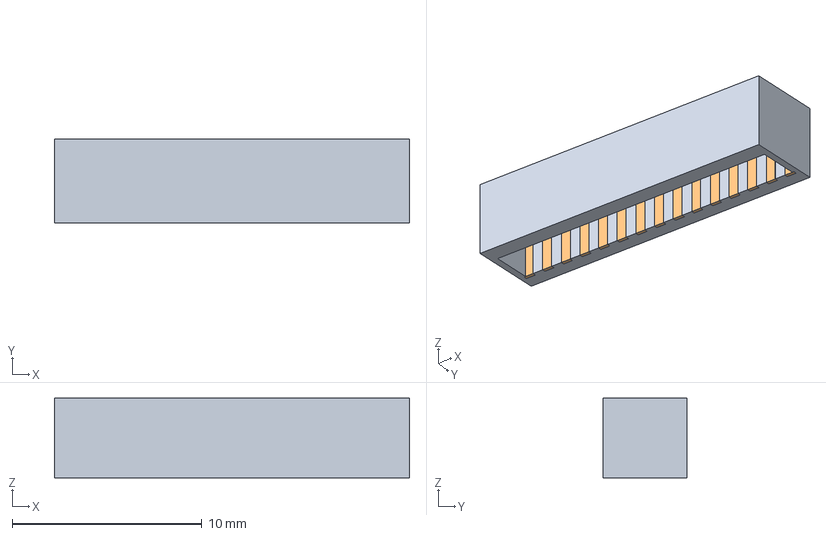
[picture p119: CAD file, 2025-10-18]
04_Hardware/PCBs/CamTracker/KiCad_Libs/Components/SHOU HAN 1.25-15P LT/SHOUHAN_1x15-Shape.step
18.7 x 4.40 x 4.20 mm
