mcihangir/camtracker/04_Hardware/PCBs/CamTracker/KiCad_Libs/Components/nvme_ssd/sm3zs067u310amr1200.stp

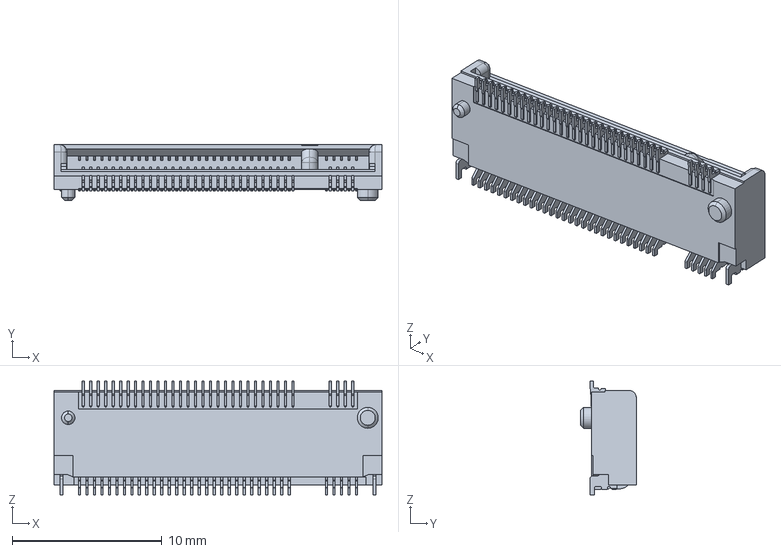
[picture p120: CAD file, 2025-10-29]
04_Hardware/PCBs/CamTracker/KiCad_Libs/Components/nvme_ssd/sm3zs067u310amr1200.stp
21.9 x 3.72 x 7.60 mm
