mcihangir/camtracker/01_Block_Diagrams/CamTracker.pdf

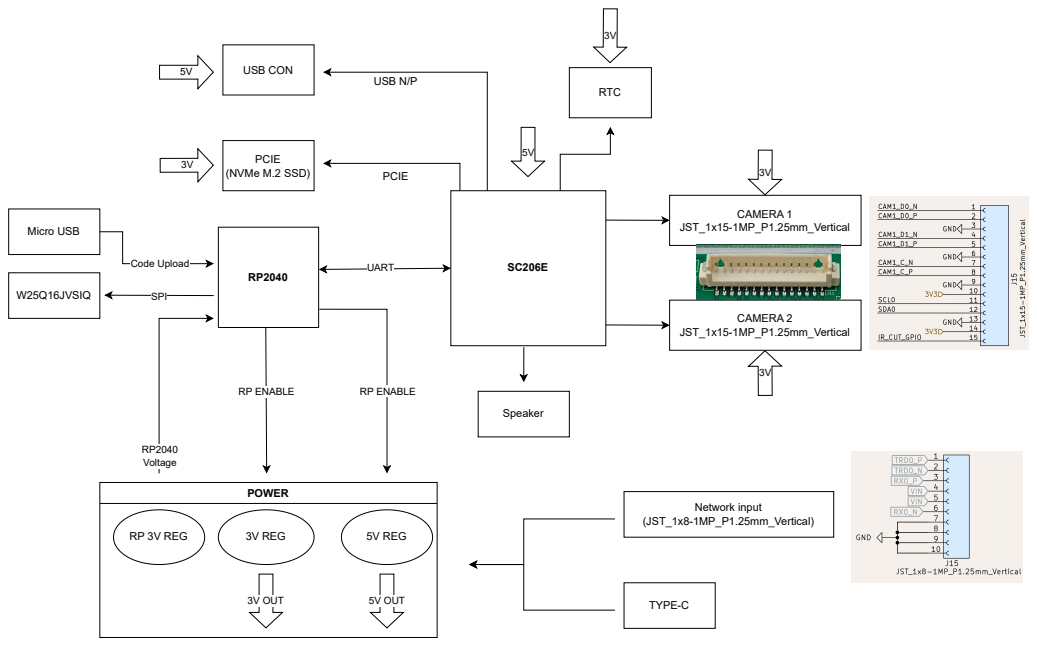
[picture p135: page 1]
TYPE-C; Network input (JST_1x8-1MP_P1.25mm_Vertical); USB CON; USB N/P; PCIE (NVMe M.2 SSD); 3V REG; 5V REG; CAMERA 1 JST_1x15-1MP_P1.25mm_Vertical; CAMERA 2 JST_1x15-1MP_P1.25mm_Vertical; RP 3V REG; UART; RTC; PCIE; RP ENABLE; RP2040 Voltage; 3V OUT; 5V OUT; POWER; Micro USB; W25Q16JVSIQ; SPI; Code Upload; Speaker
